Sadrita404/Open-Deck/Images/1.png

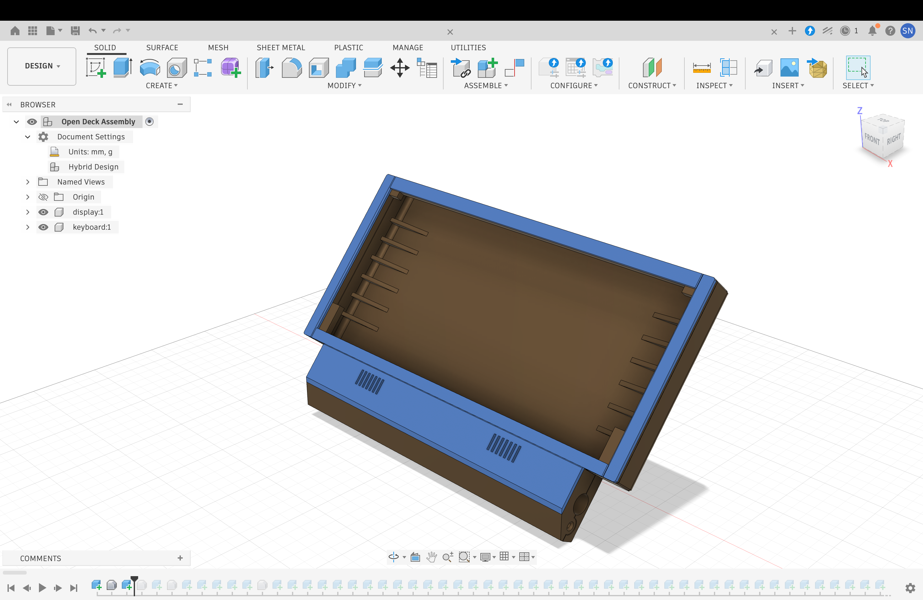
Images/1.png
