Sadrita404/Open-Deck/Images/2.png

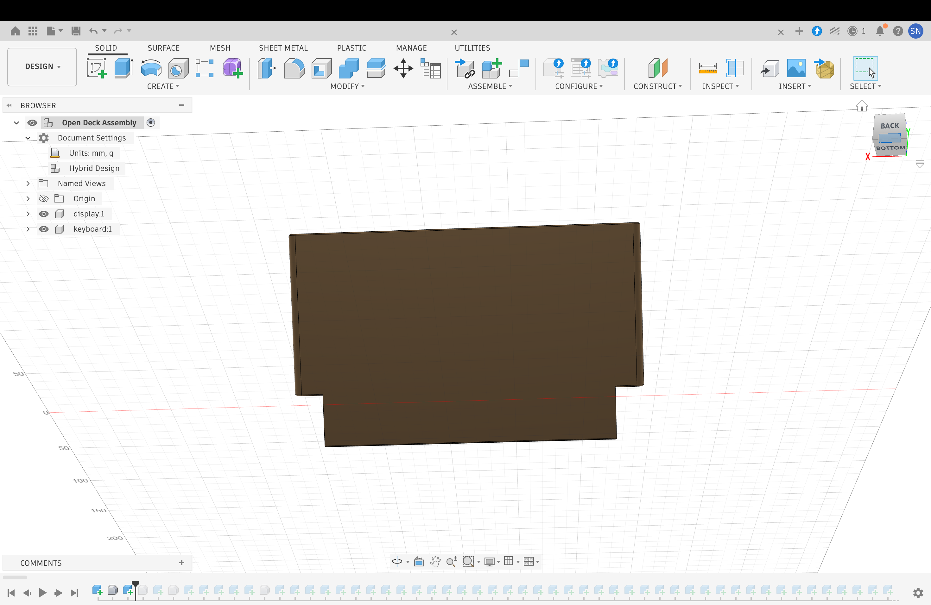
Images/2.png
