Sadrita404/Open-Deck/Images/3.png

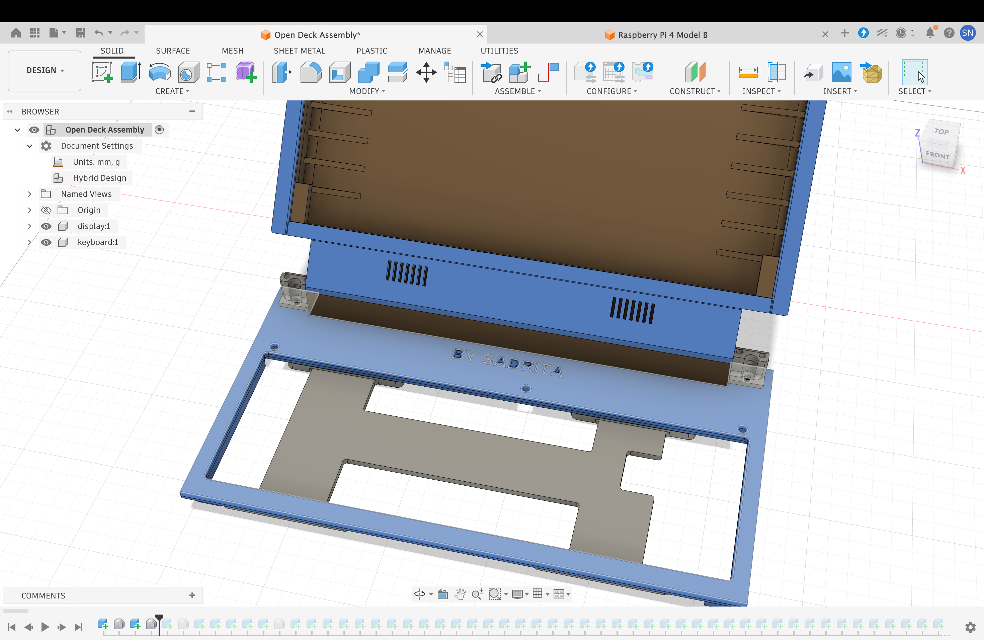
Images/3.png
