Sadrita404/Open-Deck/Images/4.png

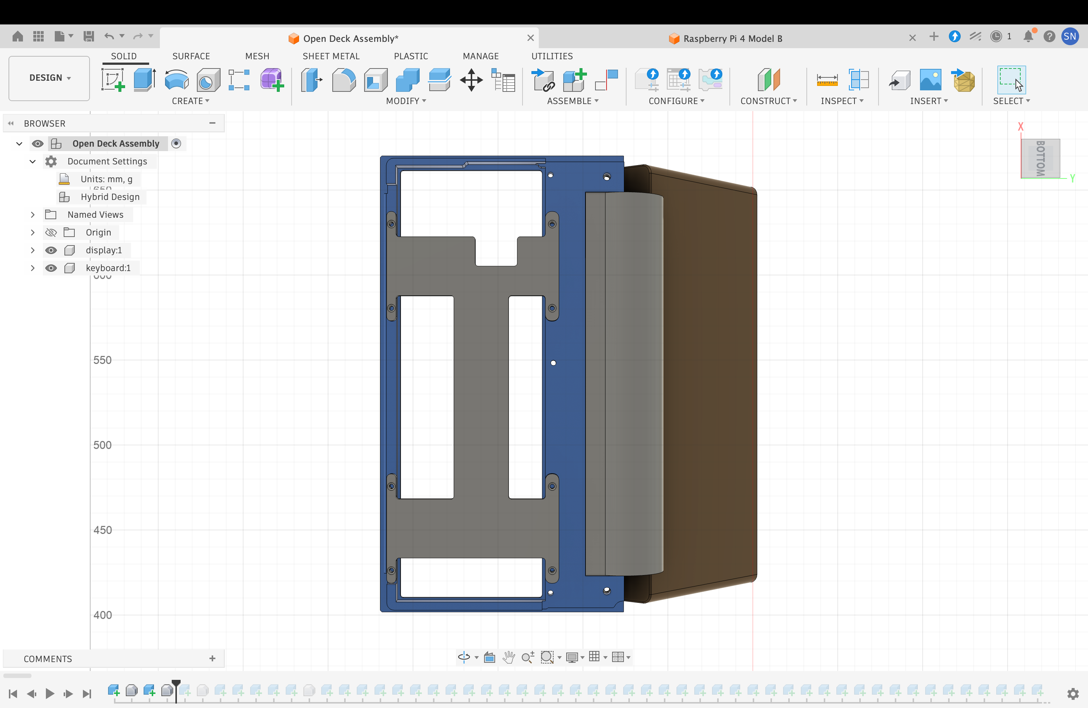
Images/4.png
