Sadrita404/Open-Deck/Images/5.png

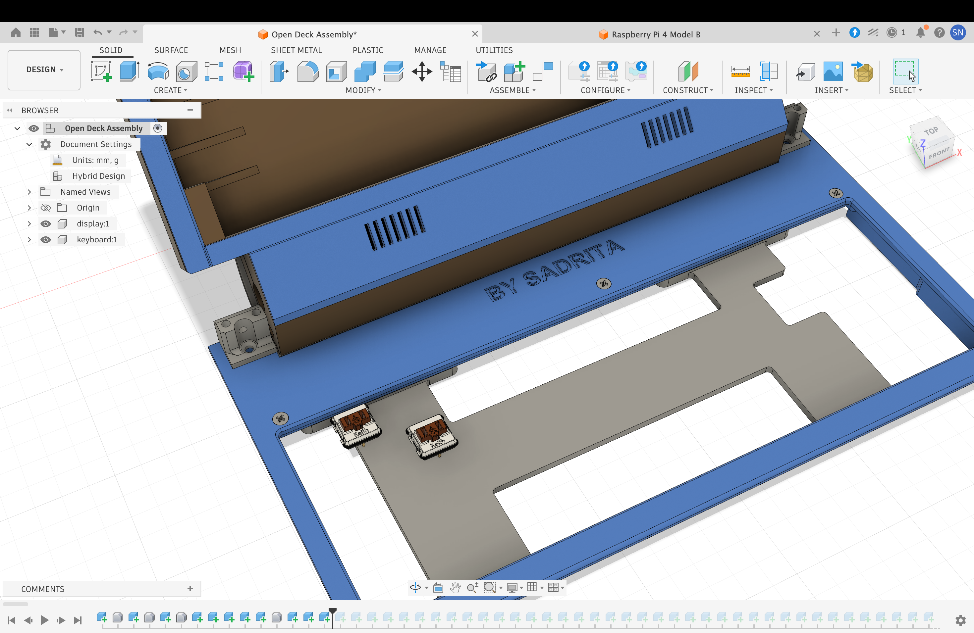
Images/5.png
