Sadrita404/Open-Deck/Images/6.png

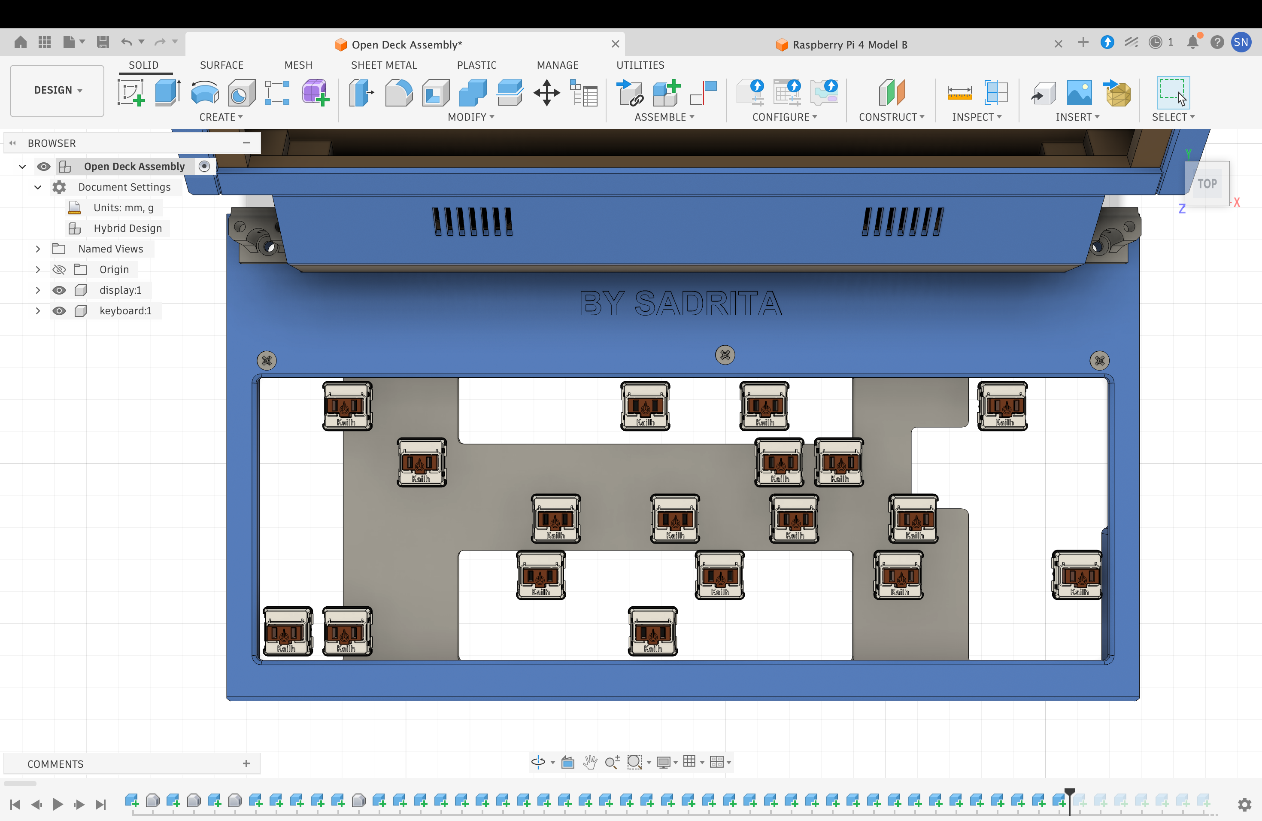
Images/6.png
