Sadrita404/Open-Deck/Images/7.png

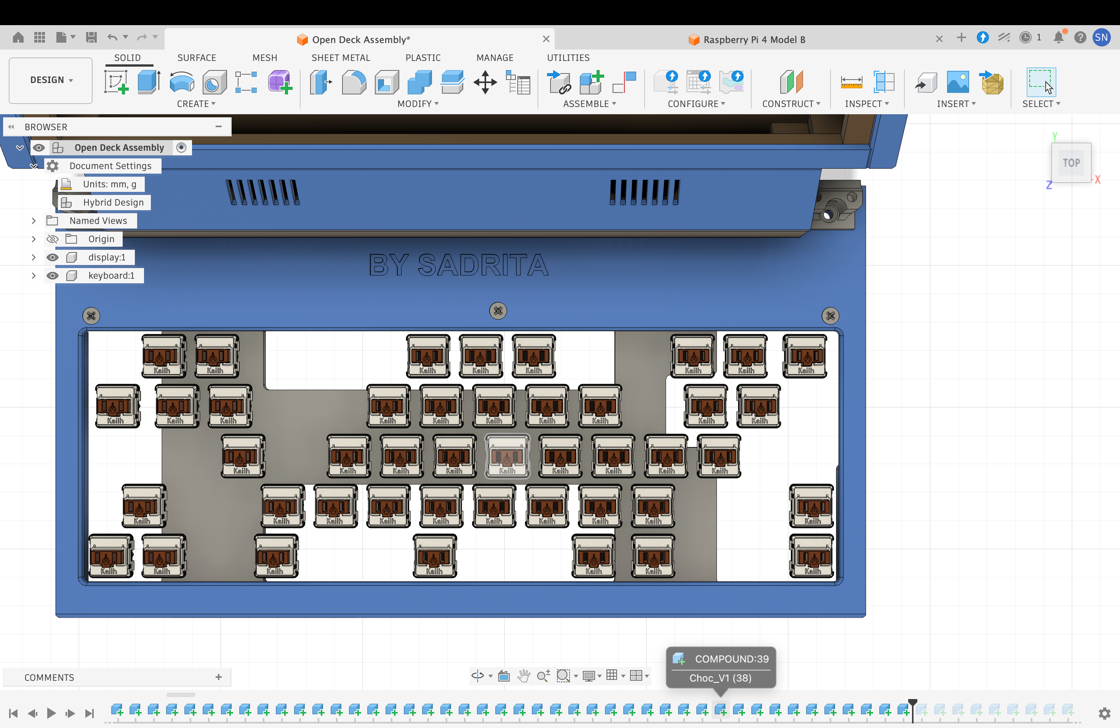
Images/7.png
