Sadrita404/Open-Deck/Images/8.png

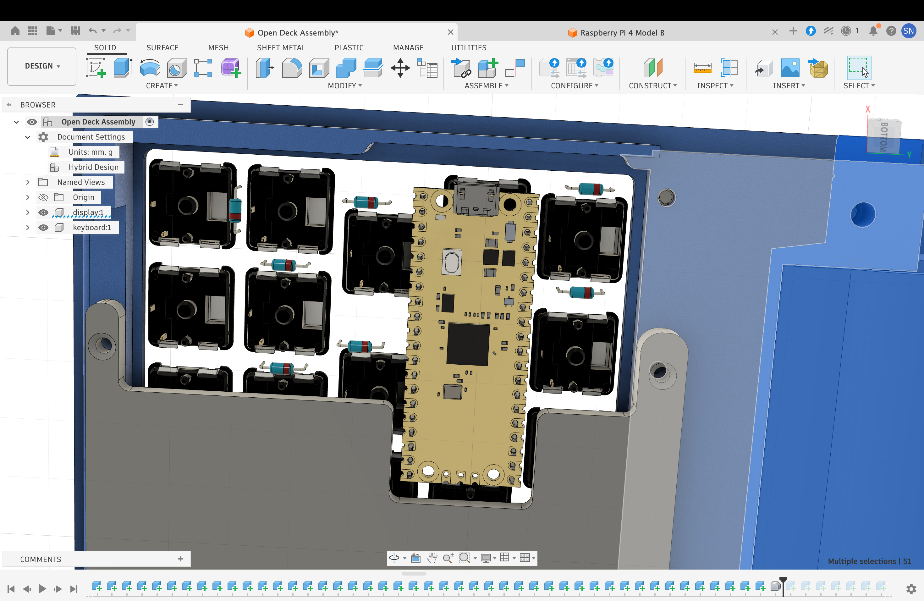
Images/8.png
