Sadrita404/Open-Deck/Images/9.png

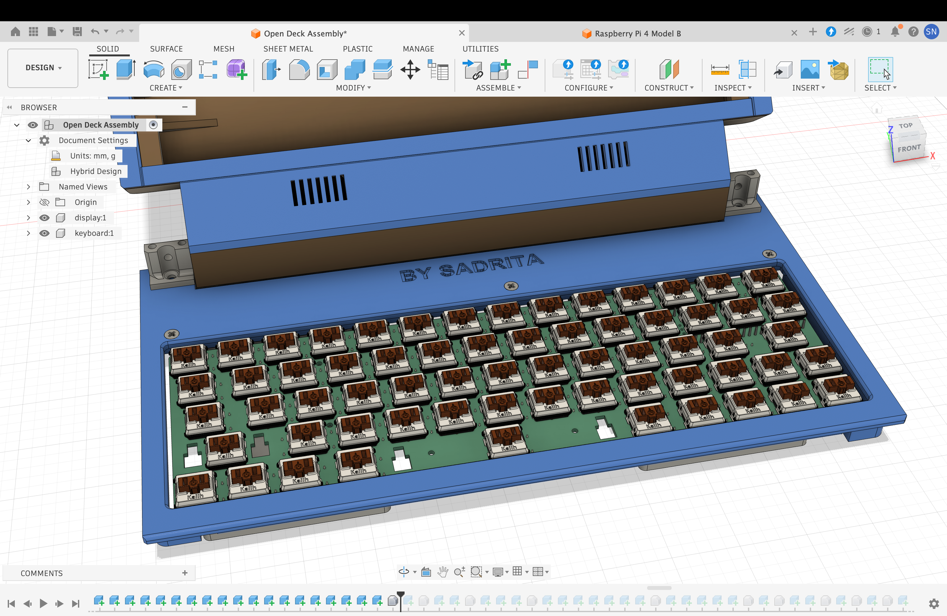
Images/9.png
