Sadrita404/Open-Deck/Images/10.png

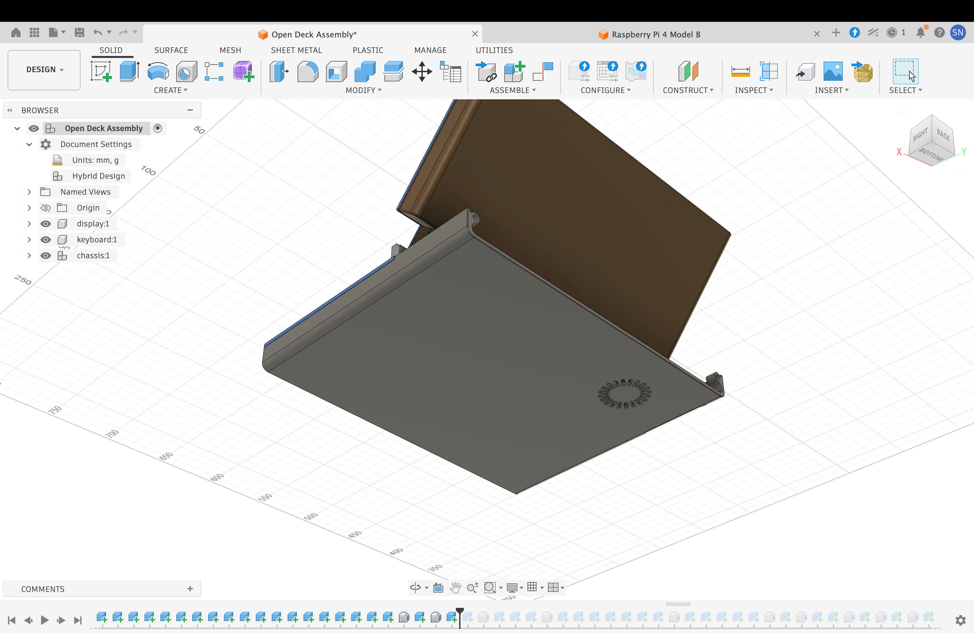
Images/10.png
