Sadrita404/Open-Deck/Images/11.png

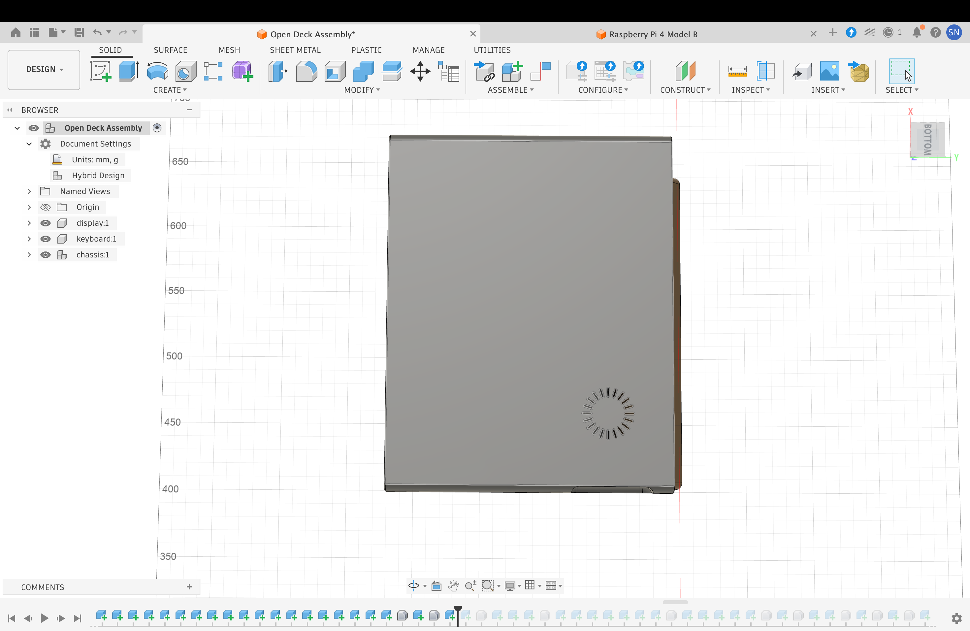
Images/11.png
