Sadrita404/Open-Deck/Images/12.png

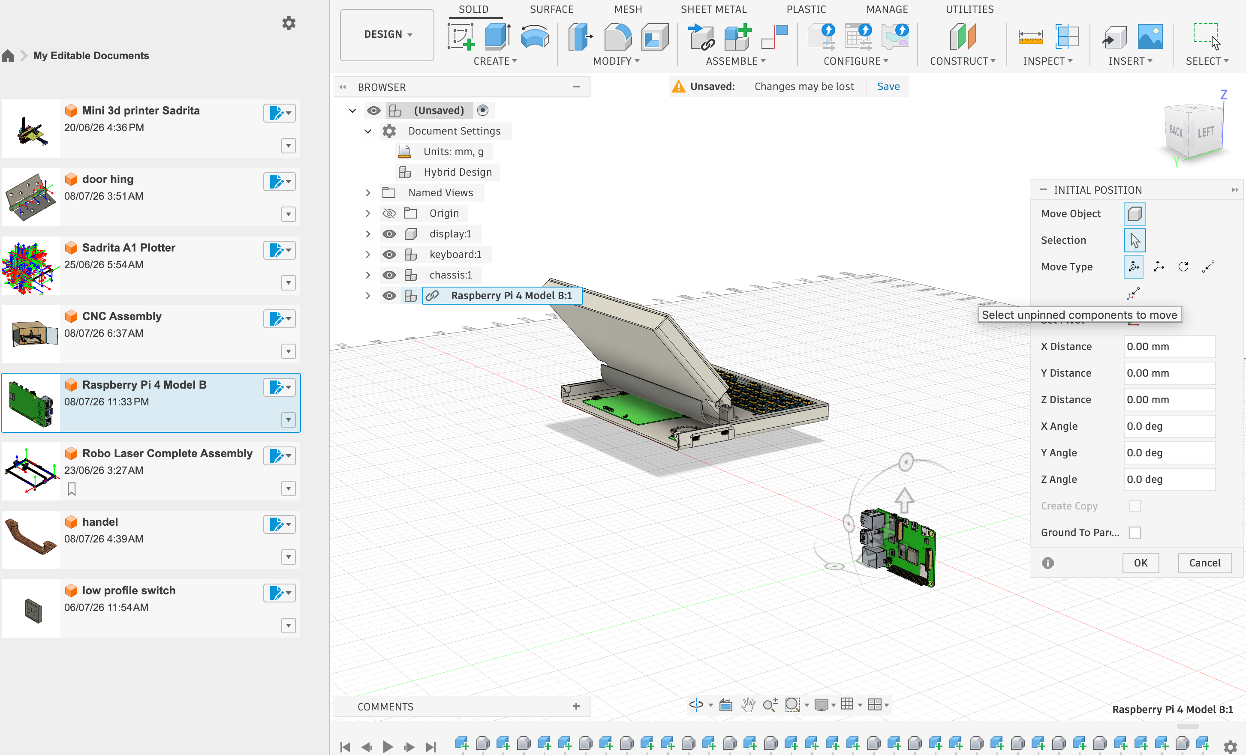
Images/12.png
