Sadrita404/Open-Deck/Images/13.png

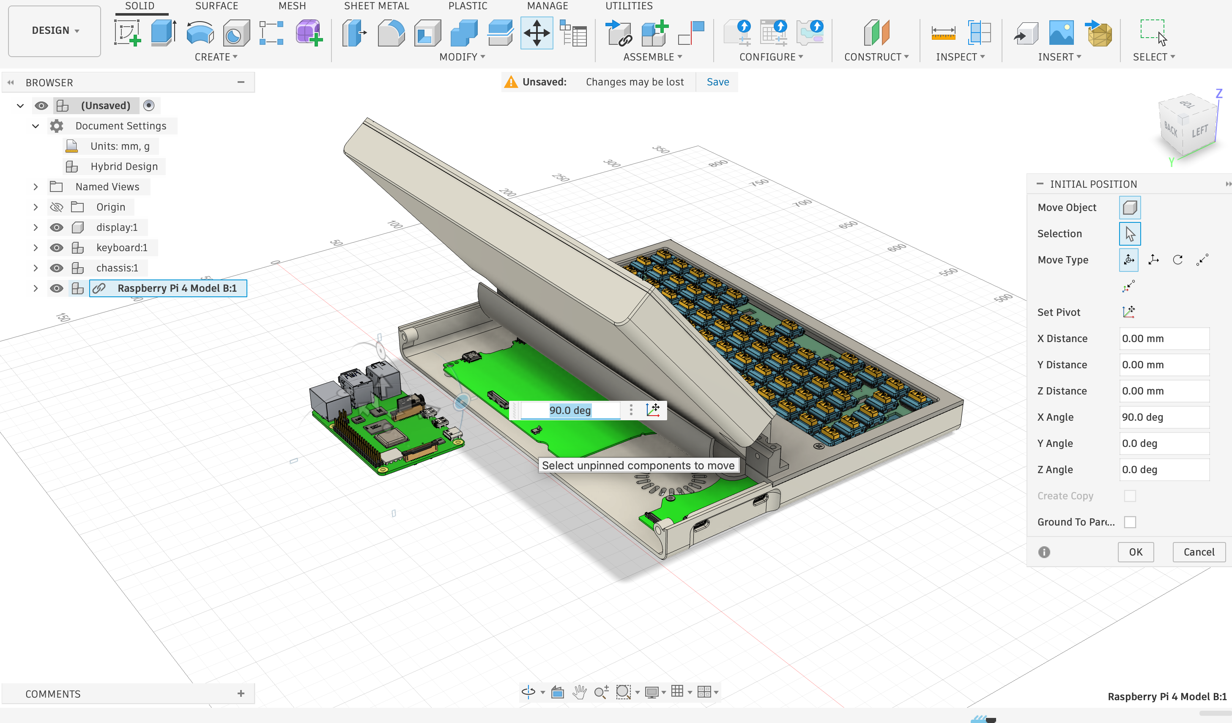
Images/13.png
