Sadrita404/Open-Deck/Images/14.png

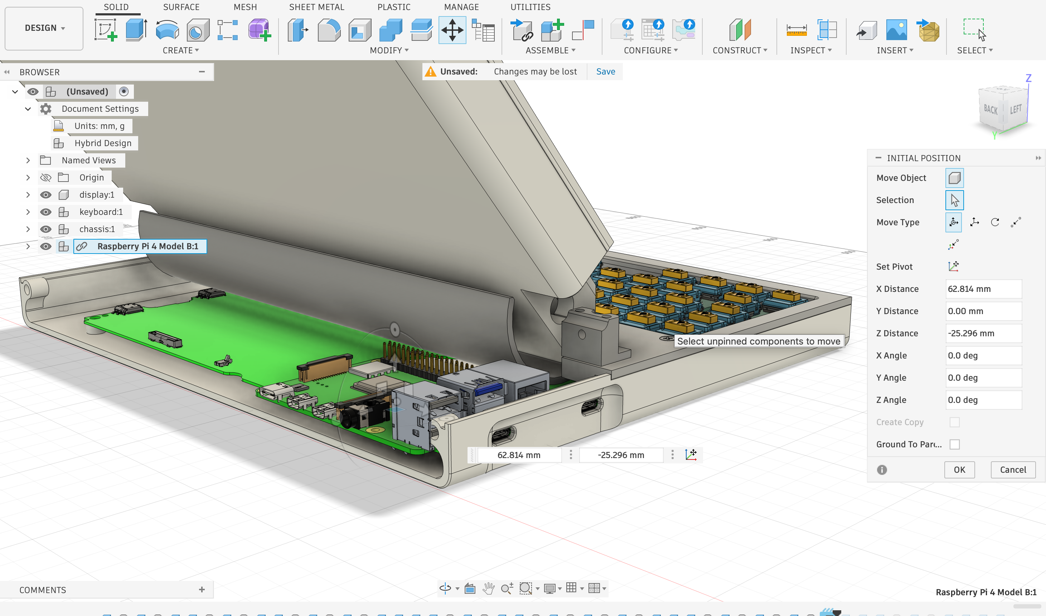
Images/14.png
