Sadrita404/Open-Deck/Images/15.png

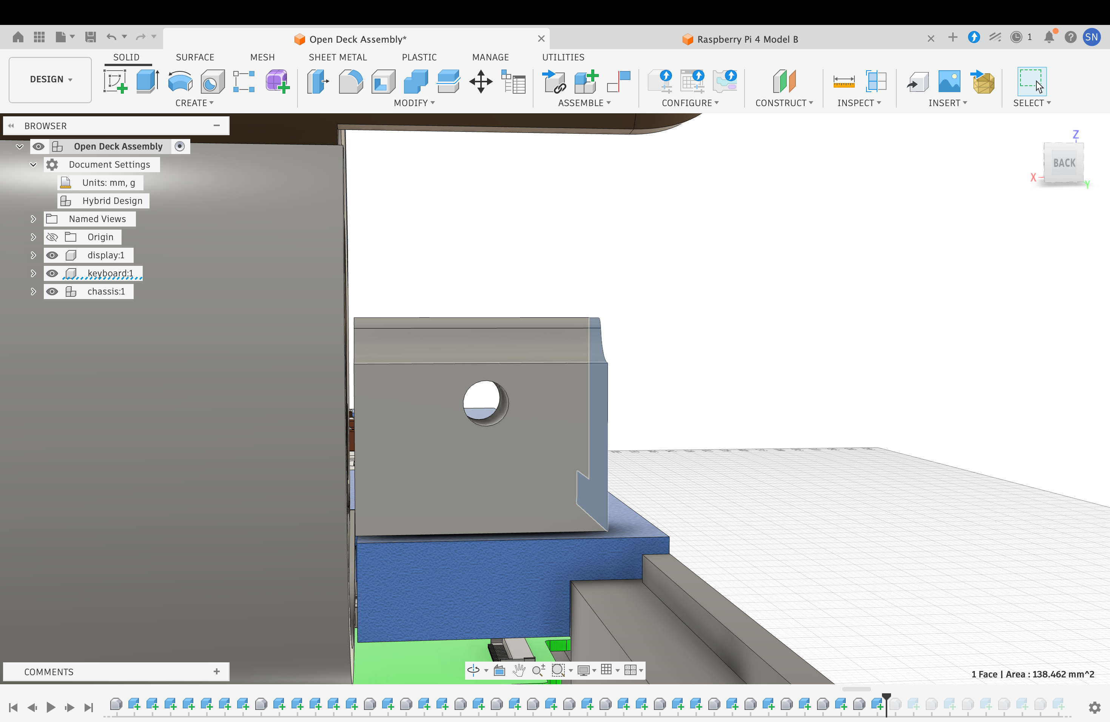
Images/15.png
