Sadrita404/Open-Deck/Images/16.png

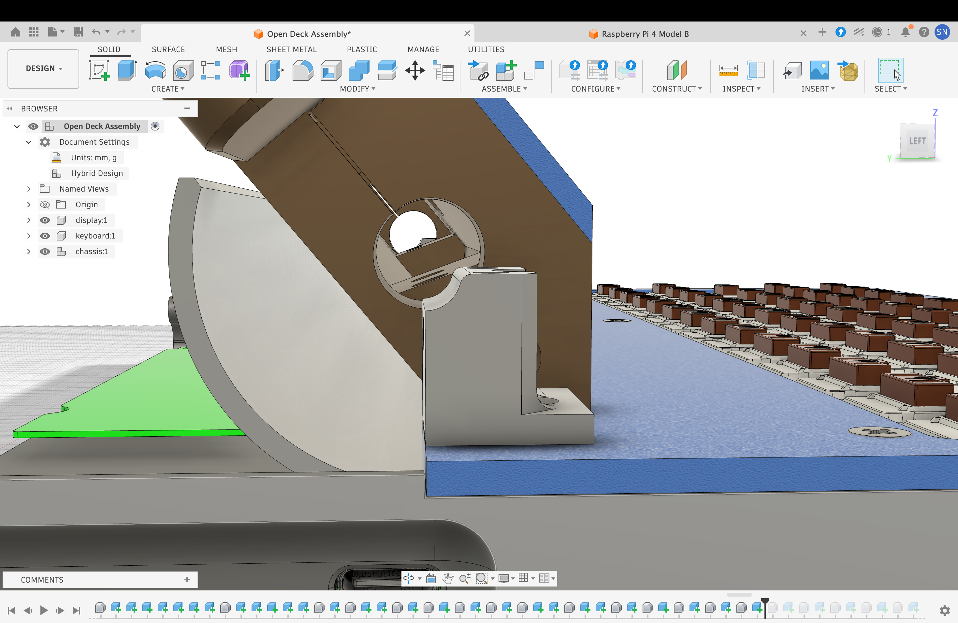
Images/16.png
