Sadrita404/Open-Deck/Images/17.png

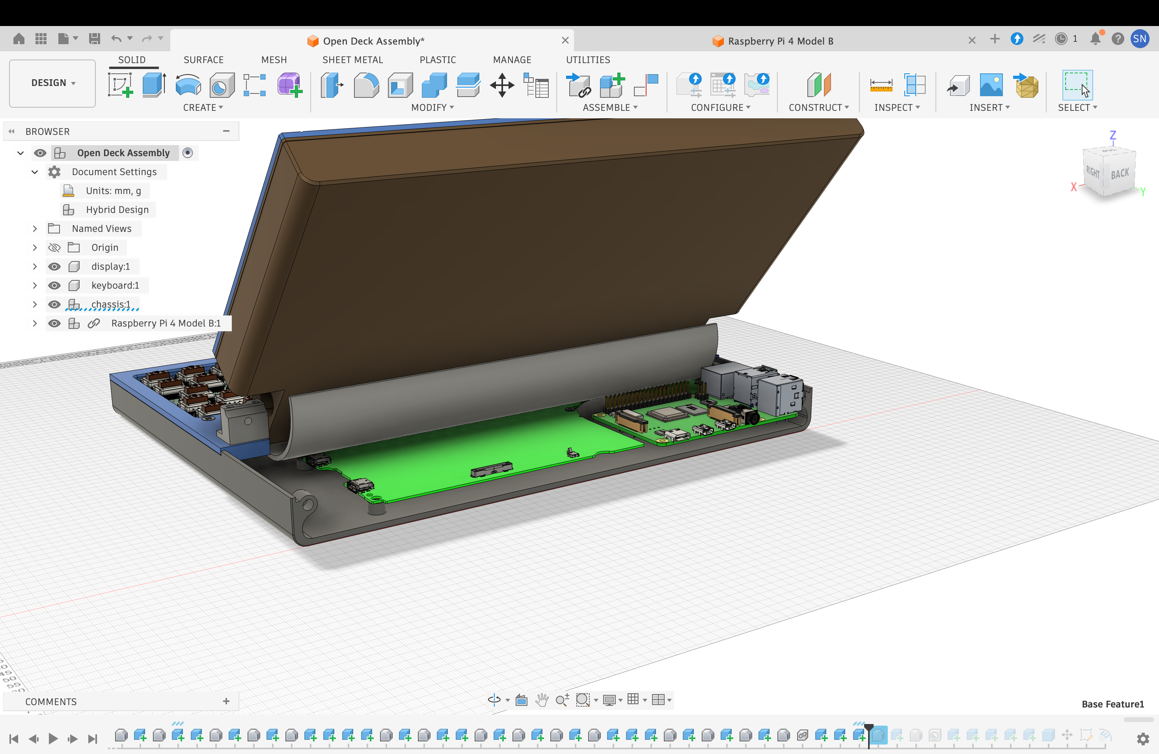
Images/17.png
