Sadrita404/Open-Deck/Images/18.png

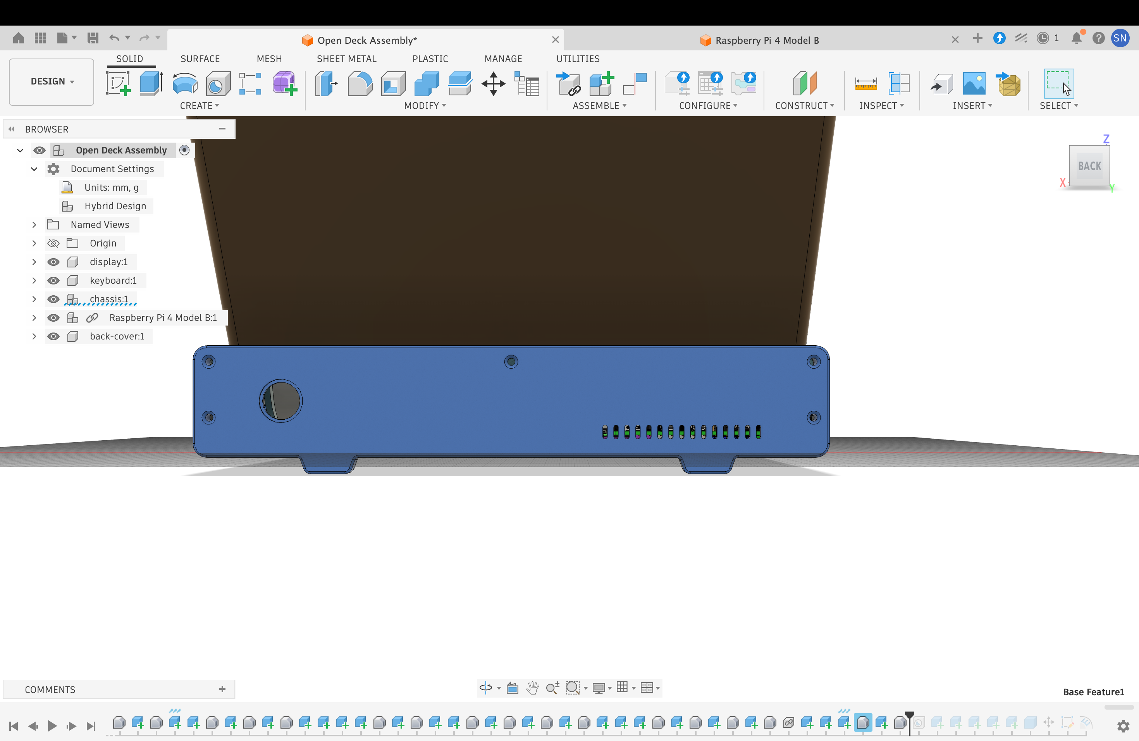
Images/18.png
