Sadrita404/Open-Deck/Images/19.png

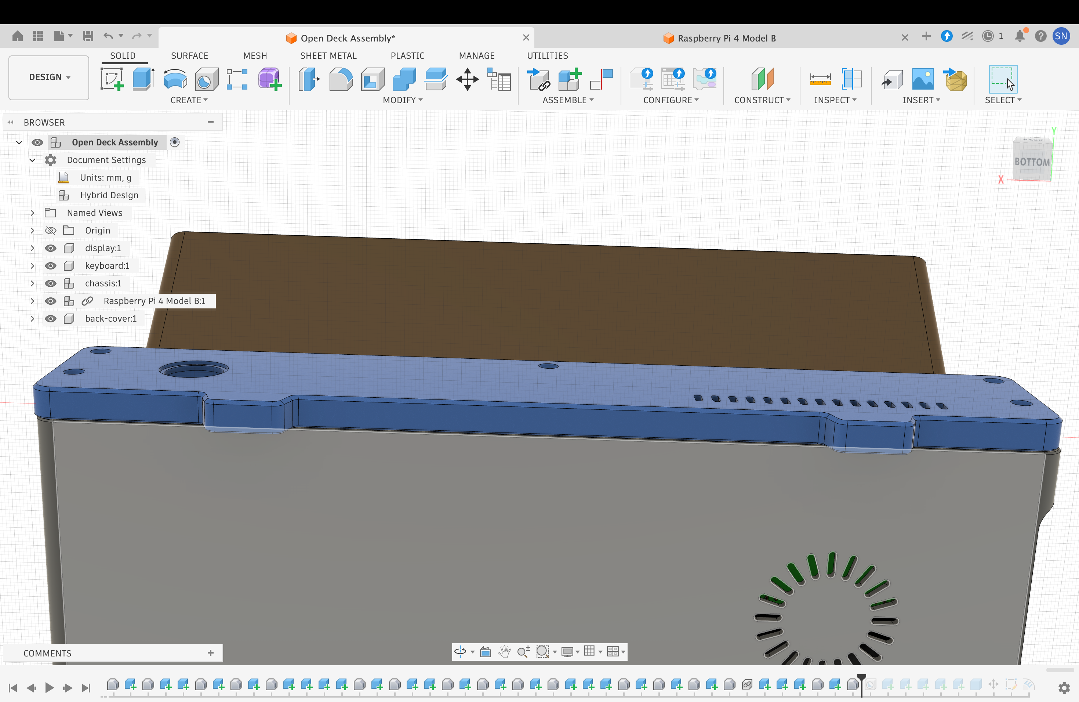
Images/19.png
