Sadrita404/Open-Deck/Images/20.png

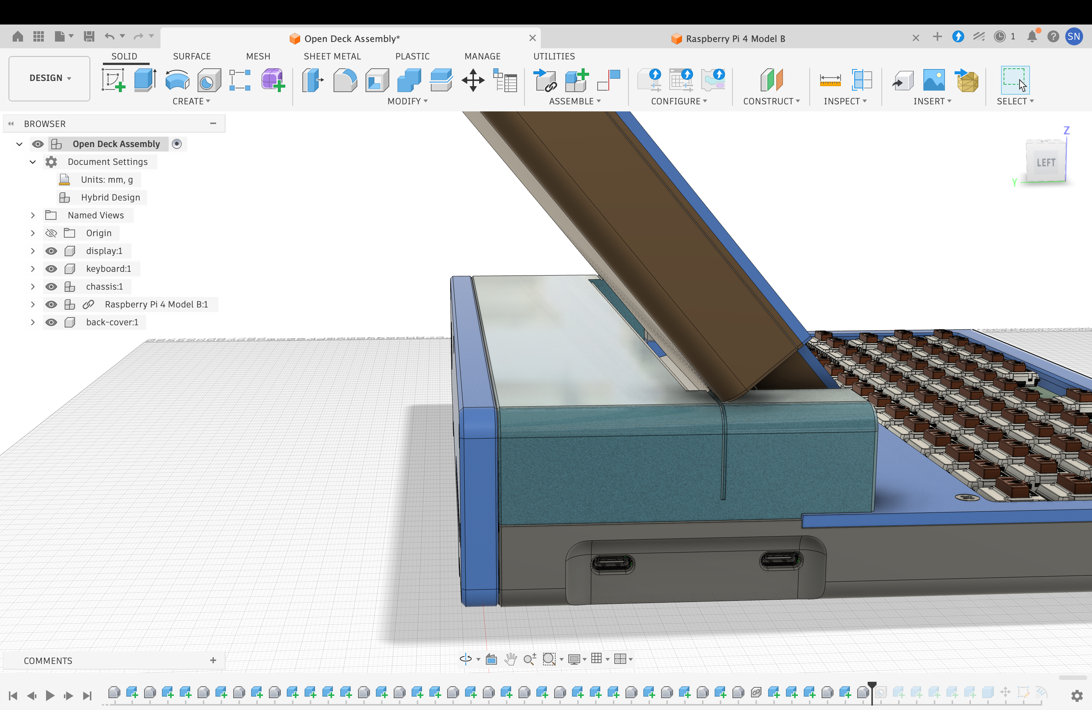
Images/20.png
