Sadrita404/Open-Deck/Images/22.png

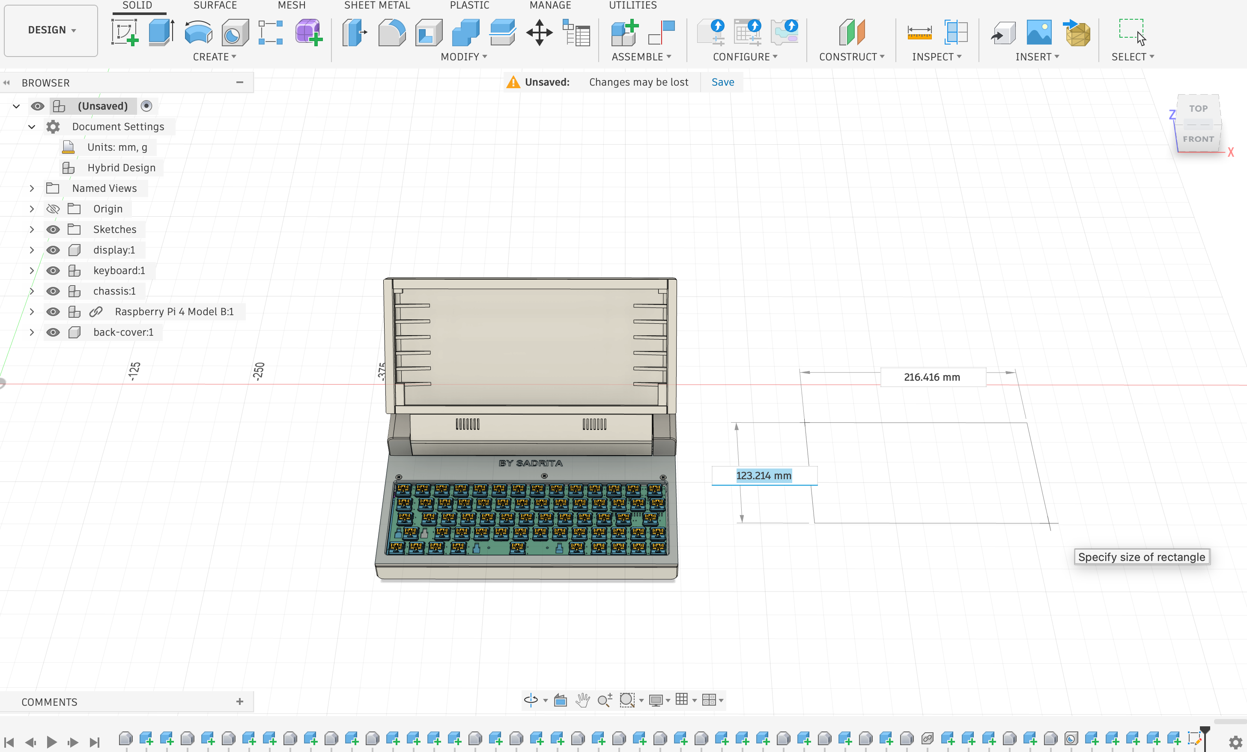
Images/22.png
