Sadrita404/Open-Deck/Images/23.png

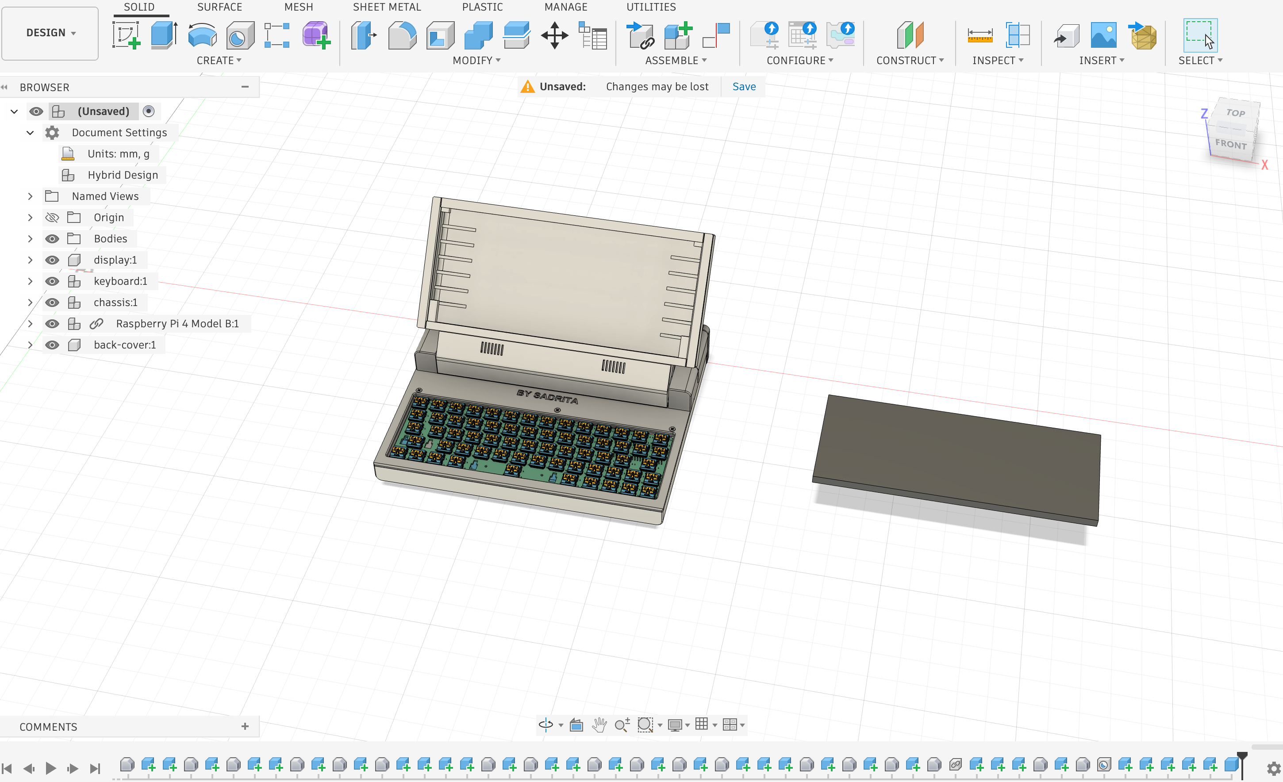
Images/23.png
