Sadrita404/Open-Deck/Images/24.png

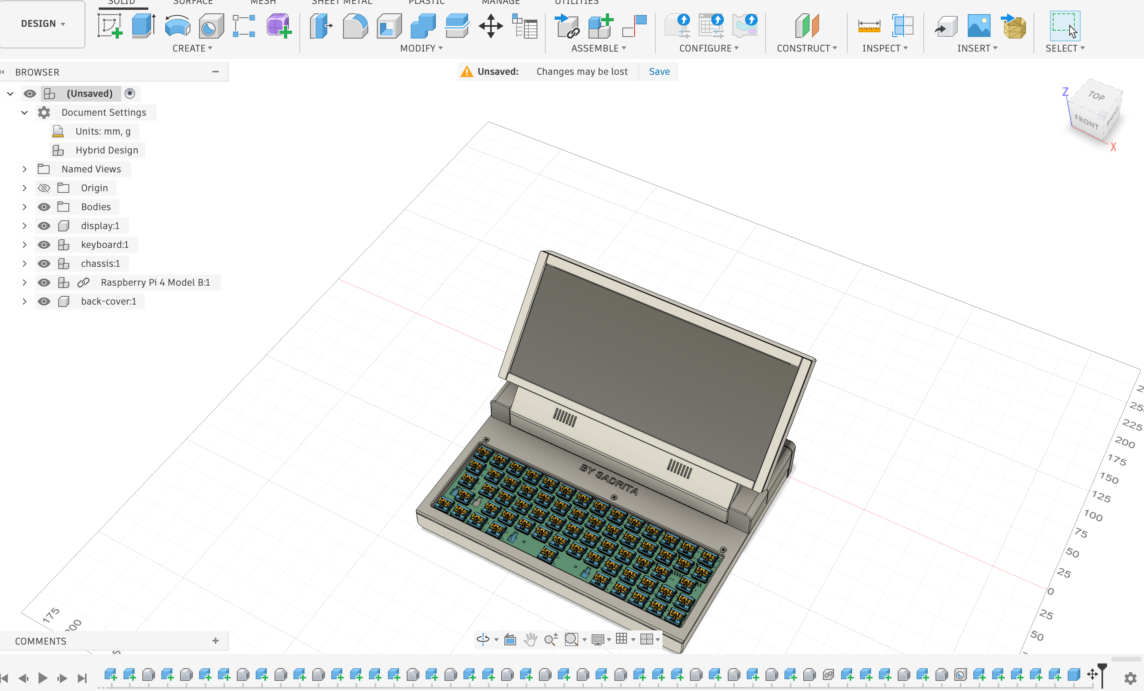
Images/24.png
