Sadrita404/Open-Deck/Images/25.png

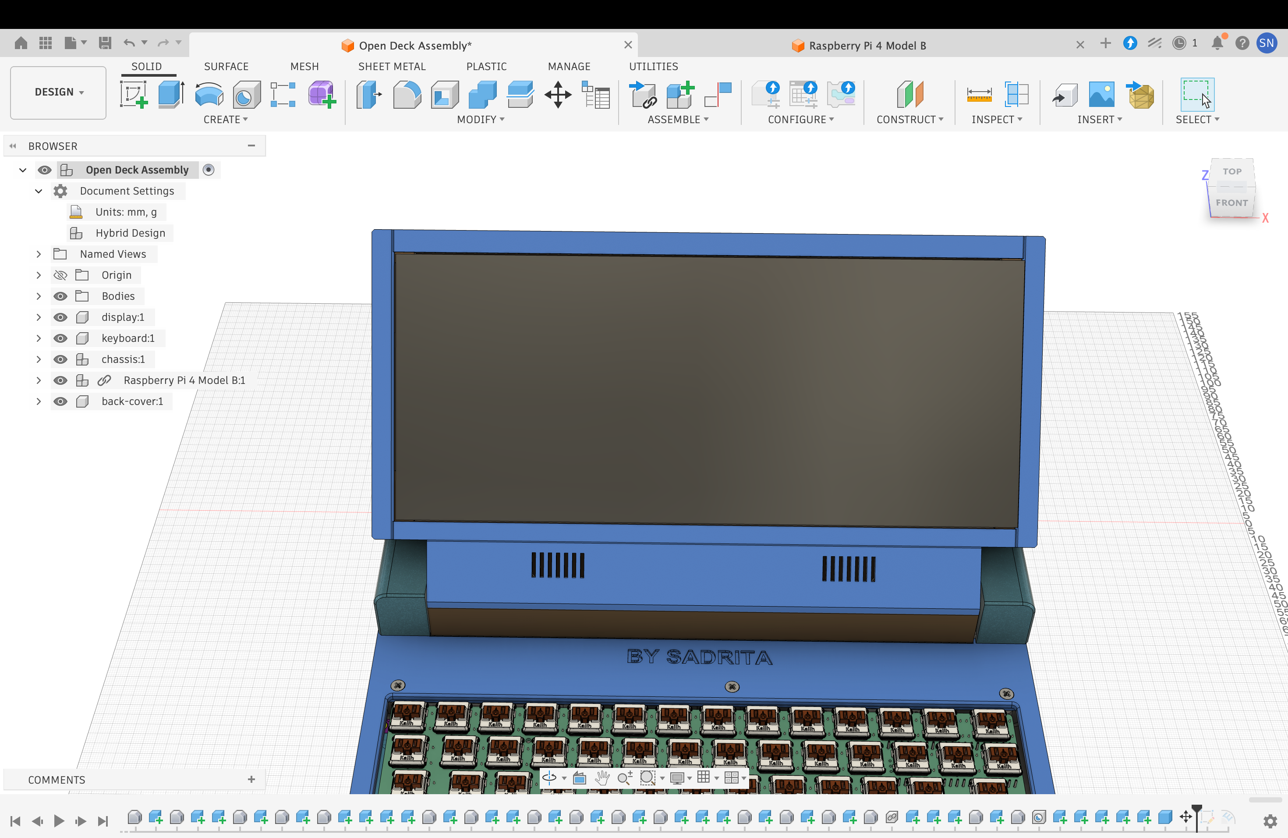
Images/25.png
