Sadrita404/Open-Deck/Images/26.png

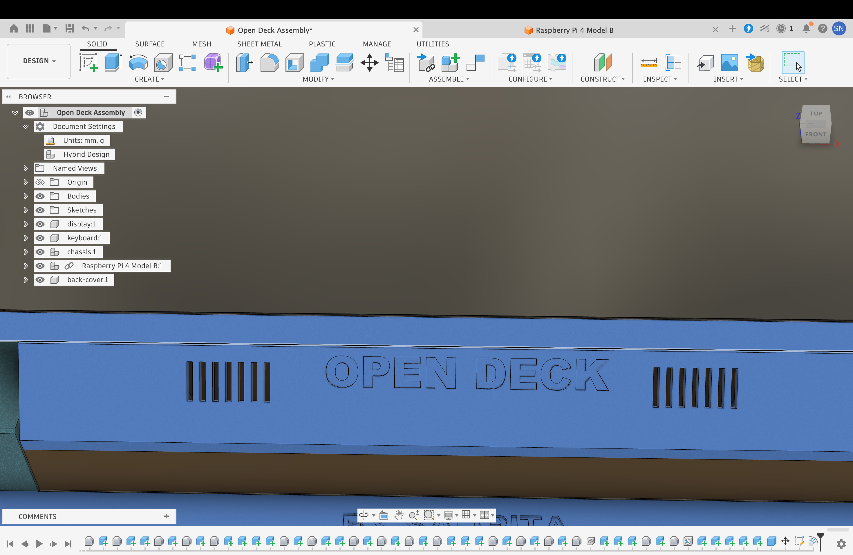
Images/26.png
