Sadrita404/Open-Deck/Images/27.png

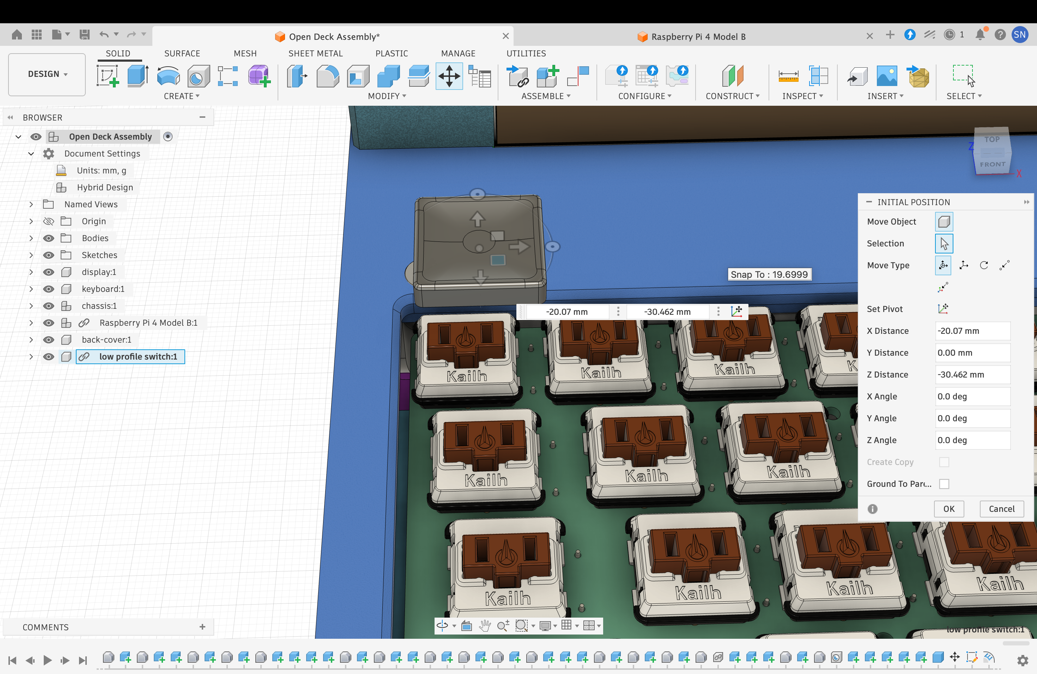
Images/27.png
