Sadrita404/Open-Deck/Images/29.png

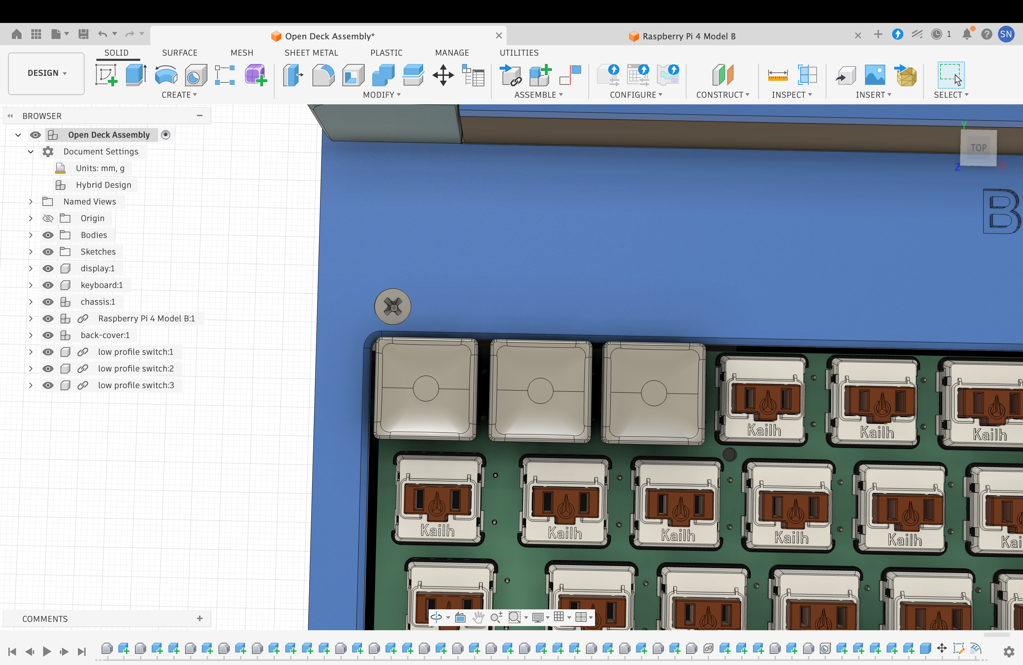
Images/29.png
