Sadrita404/Open-Deck/Images/30.png

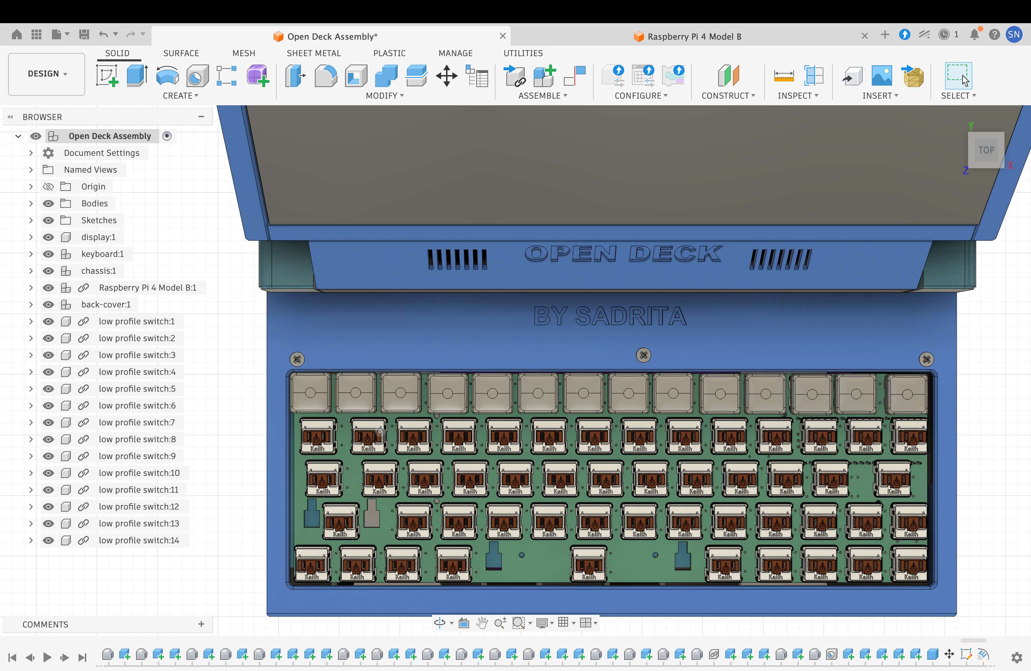
Images/30.png
