Sadrita404/Open-Deck/Images/31.png

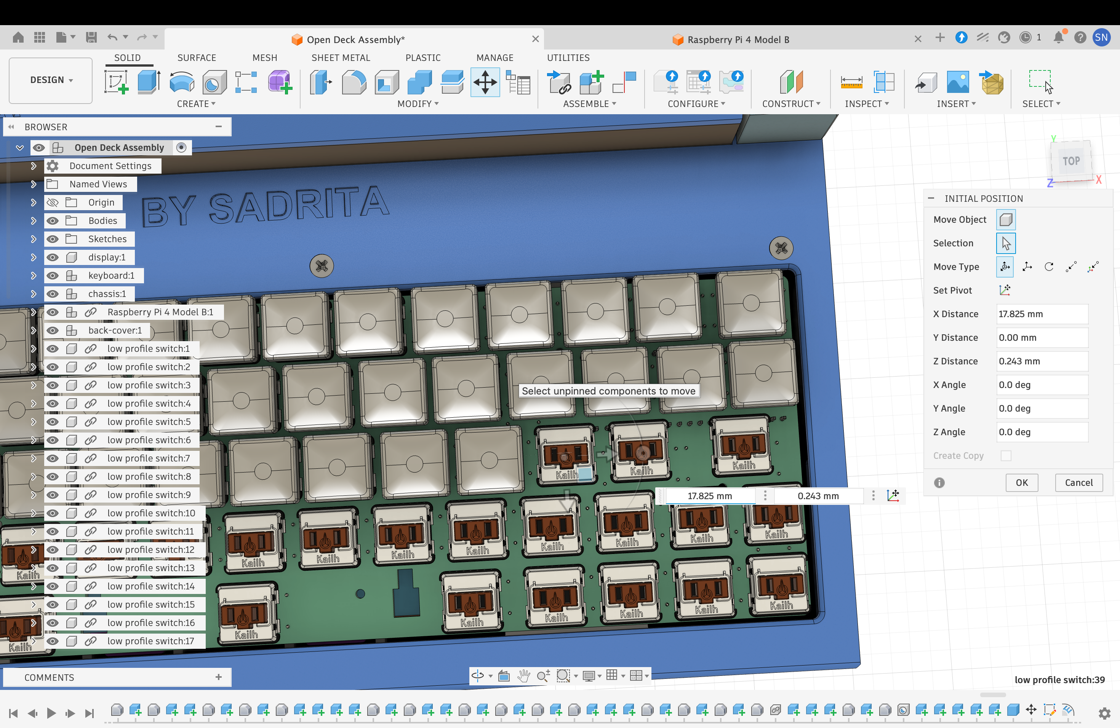
Images/31.png
