Sadrita404/Open-Deck/Images/32.png

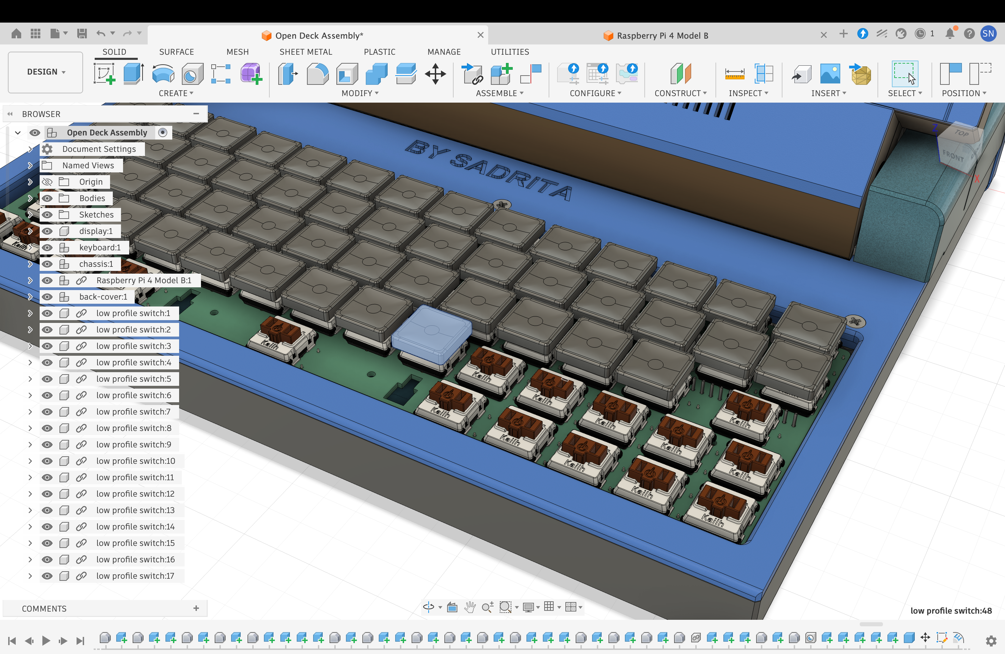
Images/32.png
