Sadrita404/Open-Deck/Images/33.png

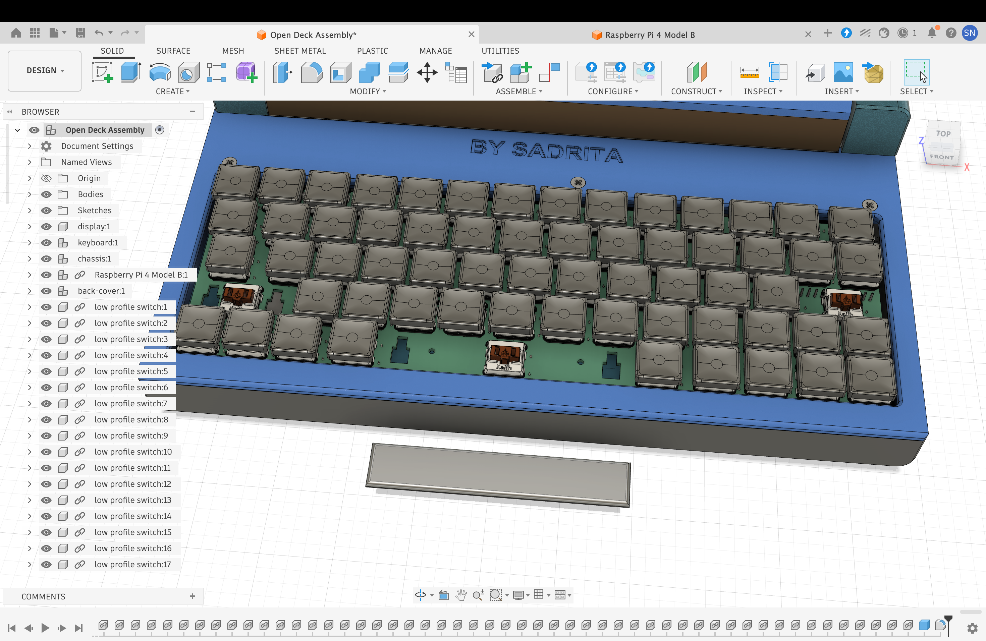
Images/33.png
