Sadrita404/Open-Deck/Images/34.png

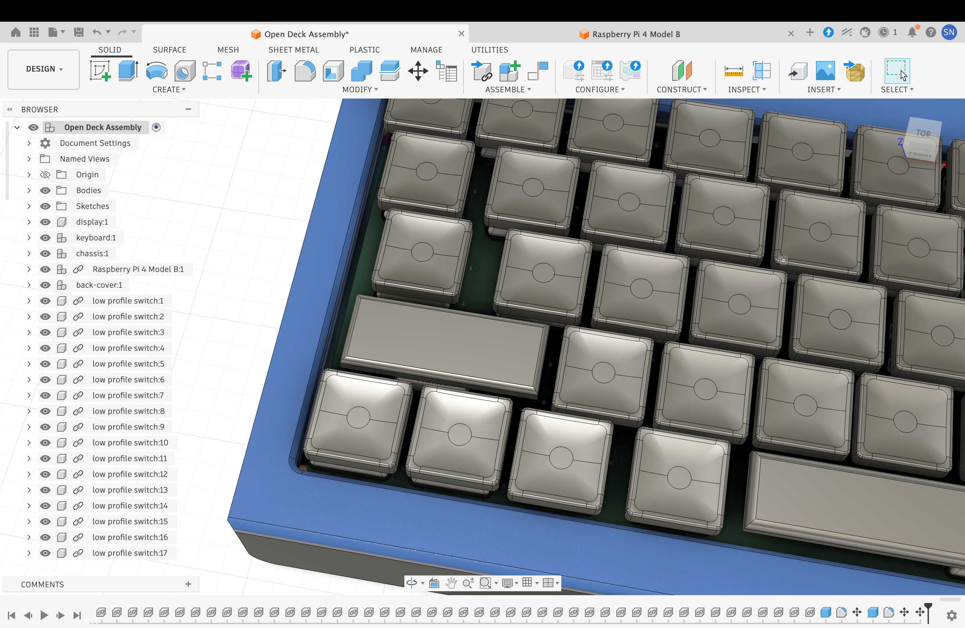
Images/34.png
