Sadrita404/Open-Deck/Images/35.png

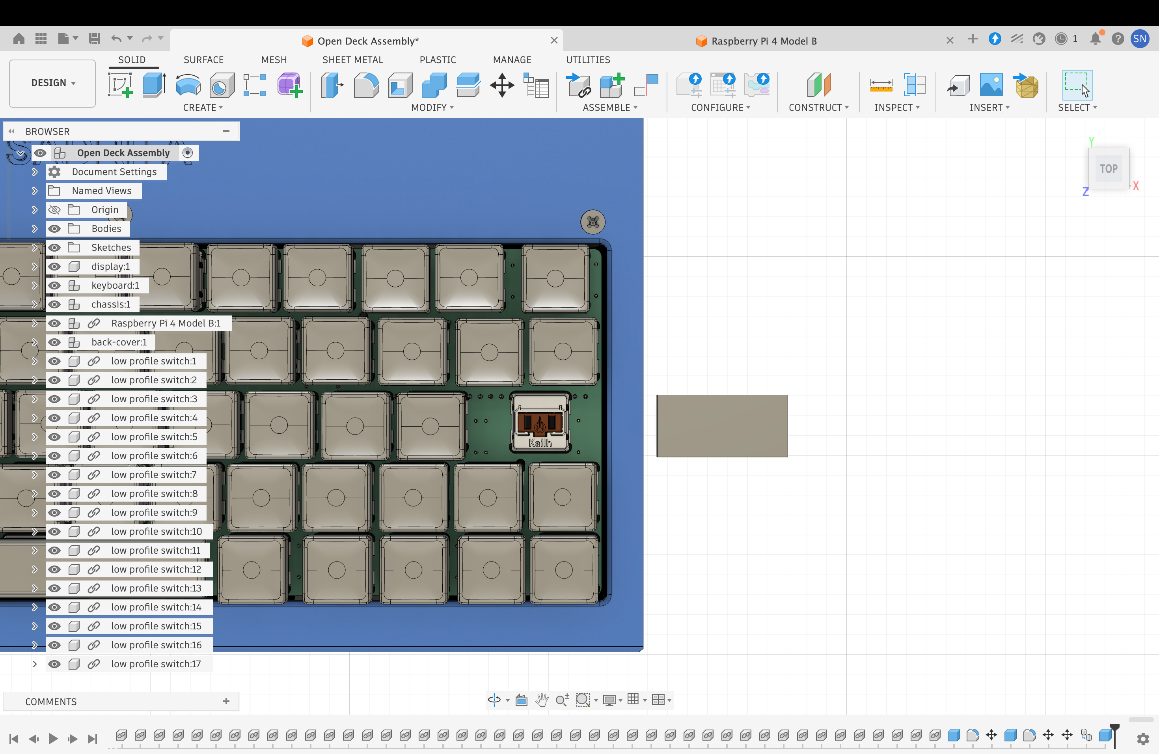
Images/35.png
