Sadrita404/Open-Deck/Images/36.png

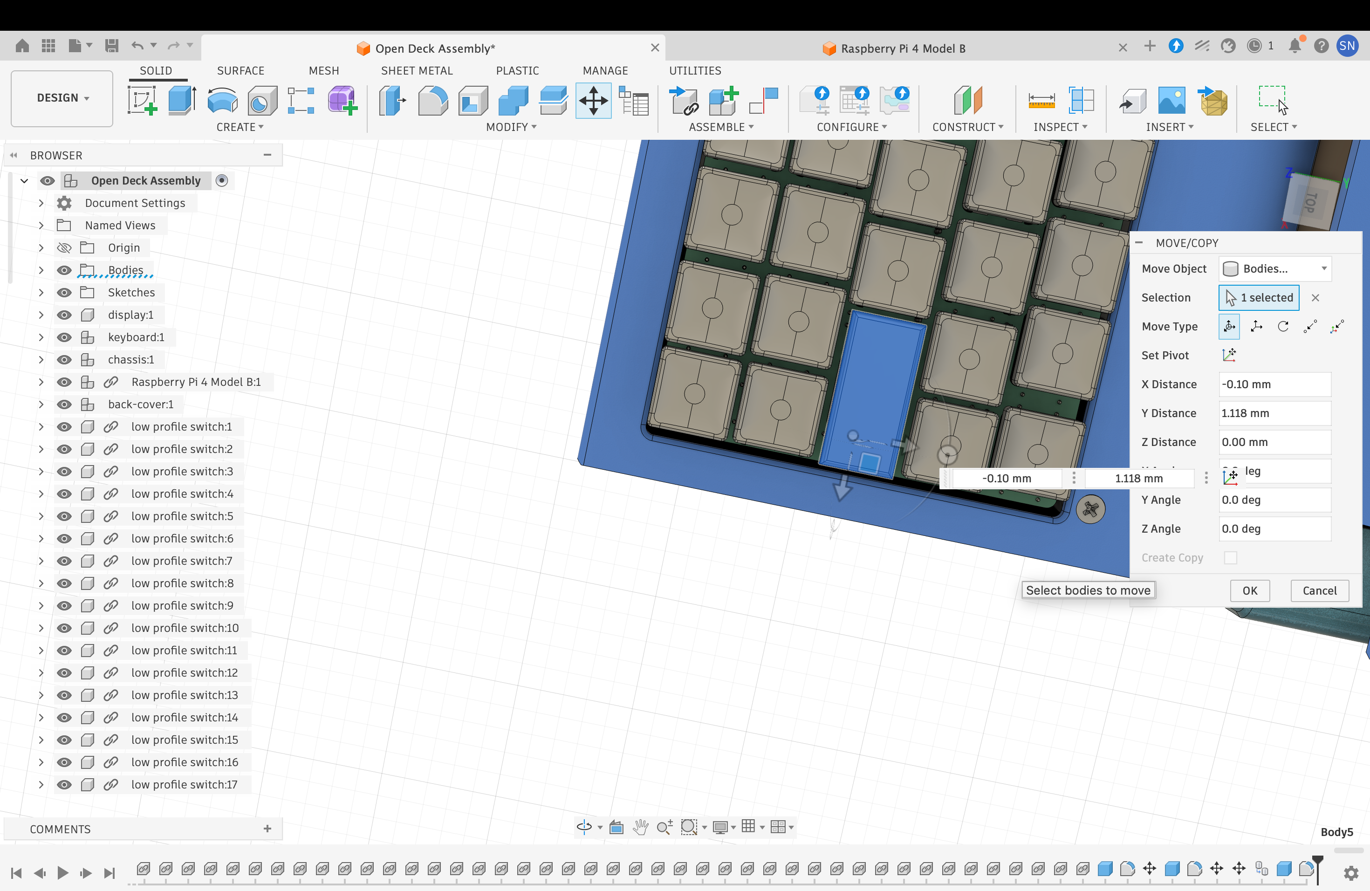
Images/36.png
