Sadrita404/Open-Deck/Images/37.png

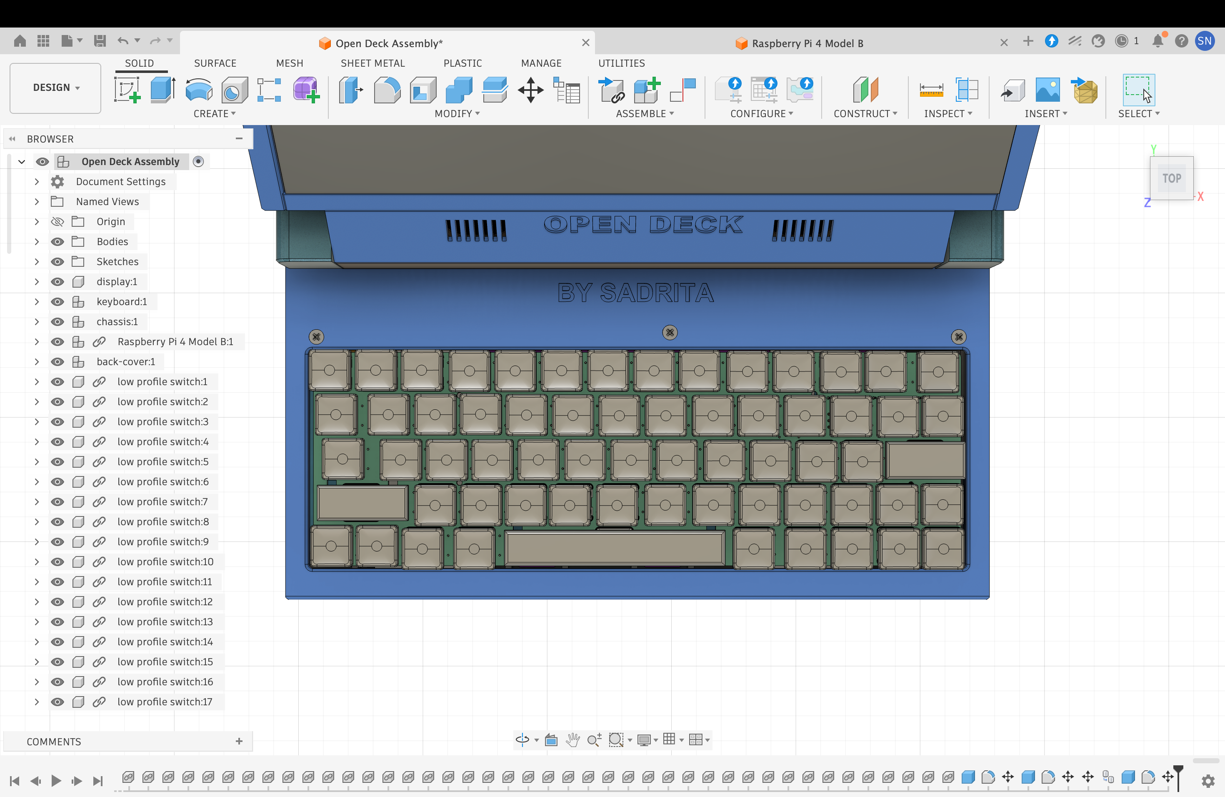
Images/37.png
