Sadrita404/Open-Deck/Images/38.png

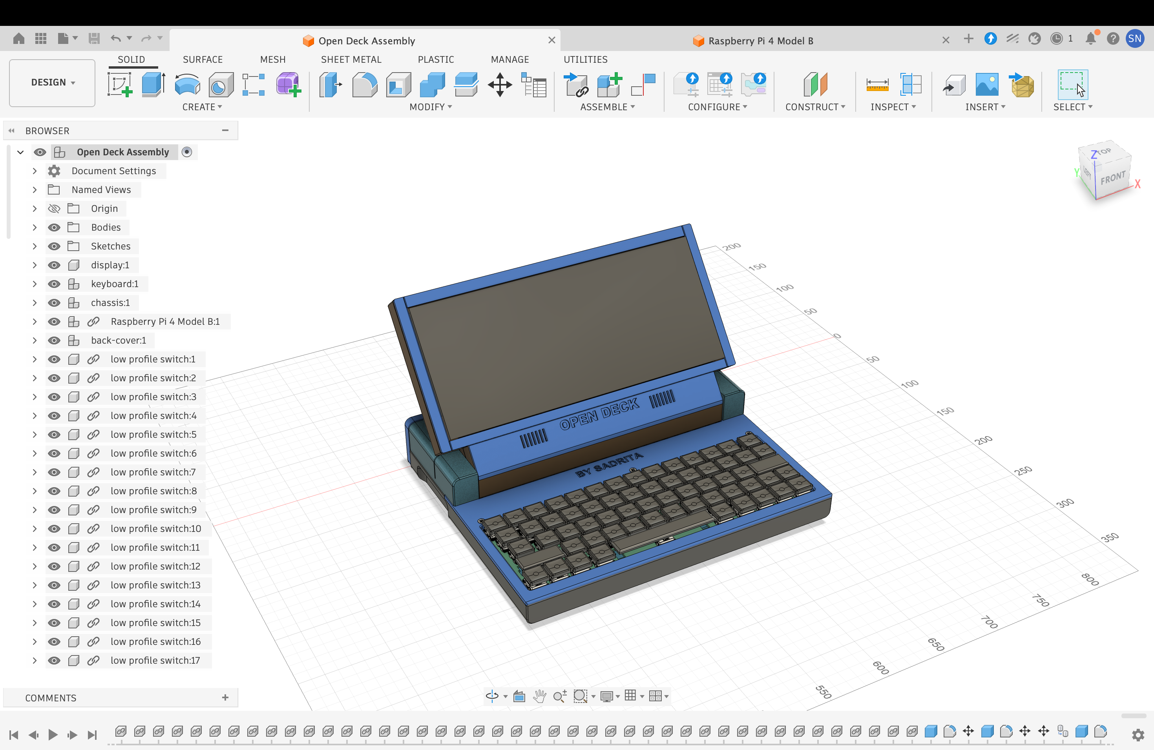
Images/38.png
