Sadrita404/Open-Deck/Images/39.png

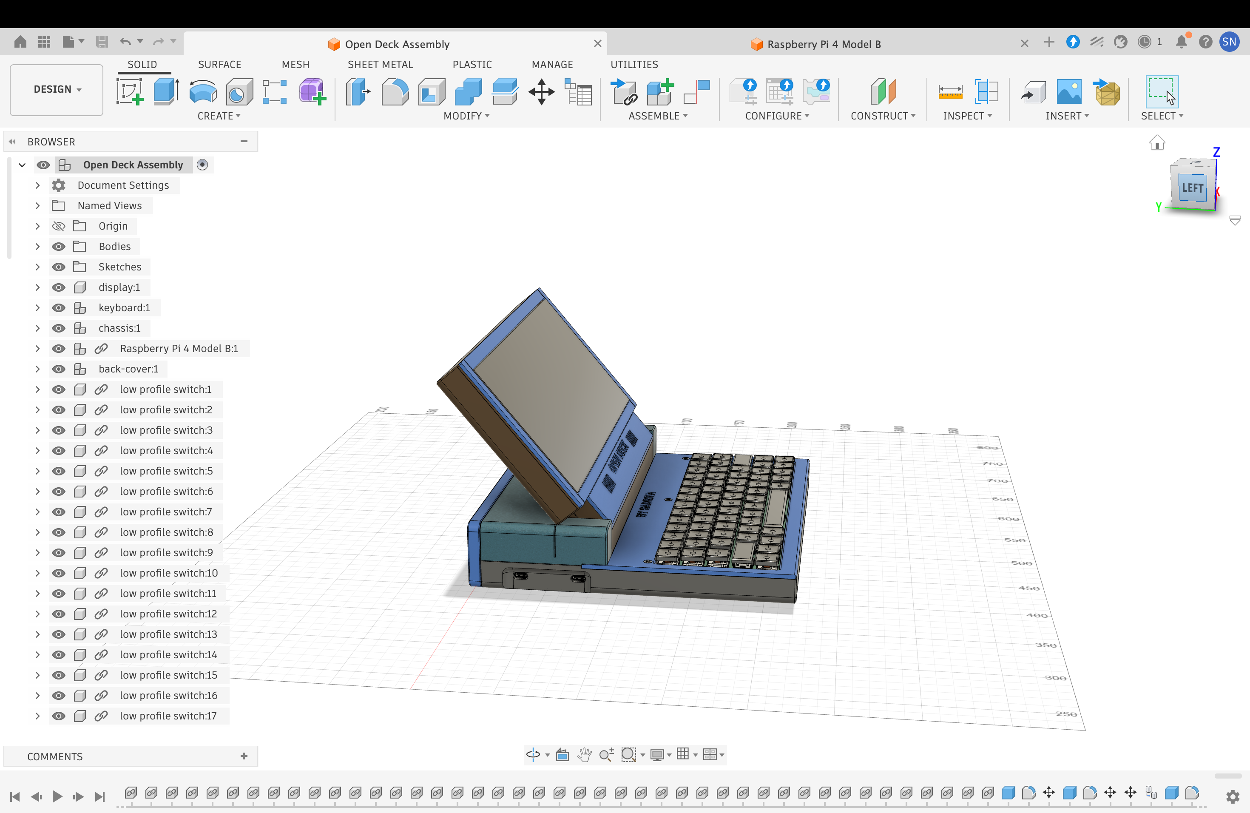
Images/39.png
