Sadrita404/Open-Deck/Images/40.png

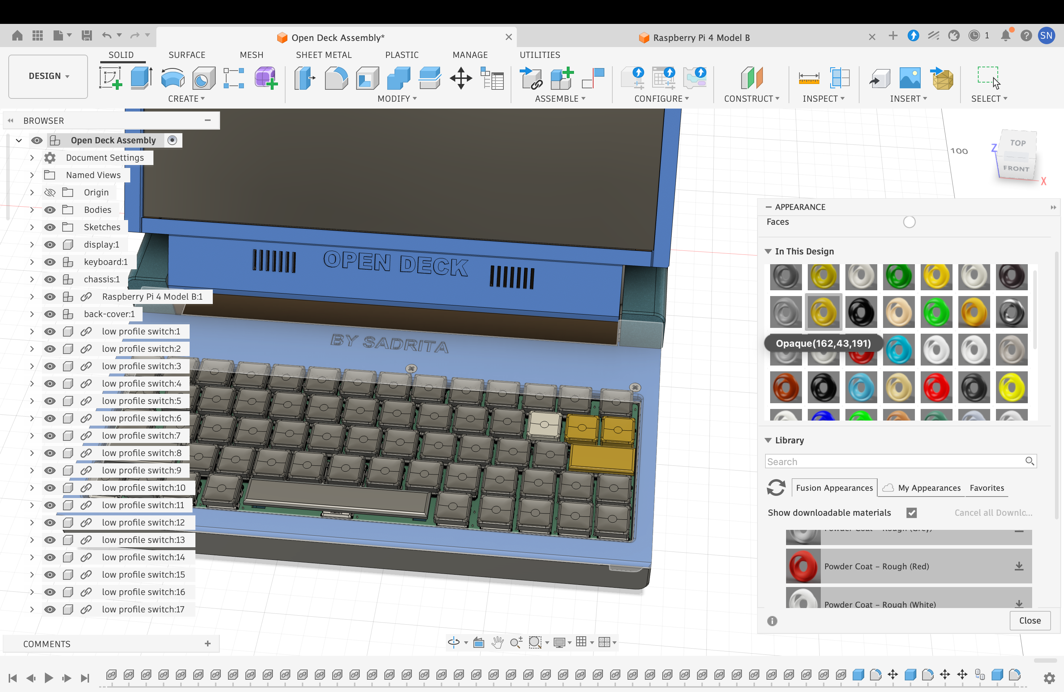
Images/40.png
