Sadrita404/Open-Deck/Images/41.png

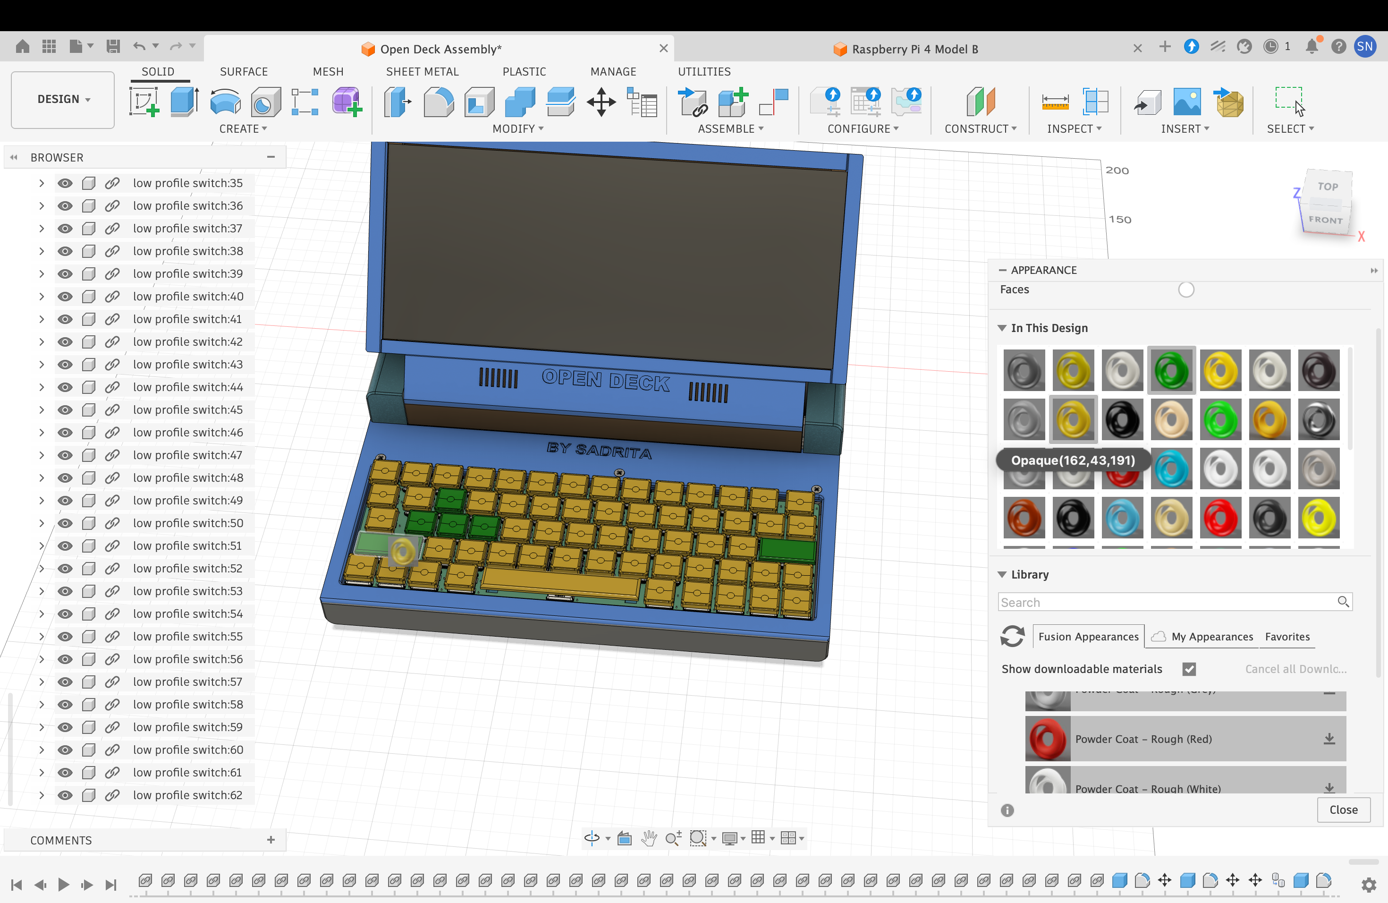
Images/41.png
