Sadrita404/Open-Deck/Images/42.png

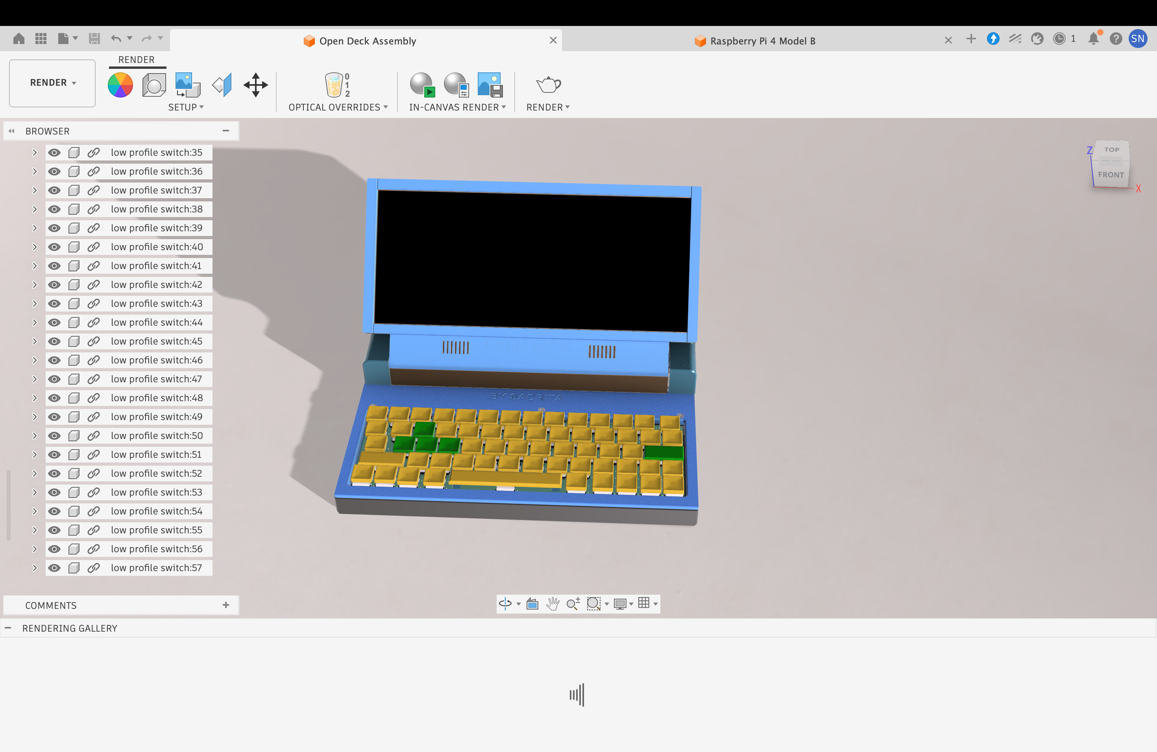
Images/42.png
