Sadrita404/Open-Deck/Images/44.png

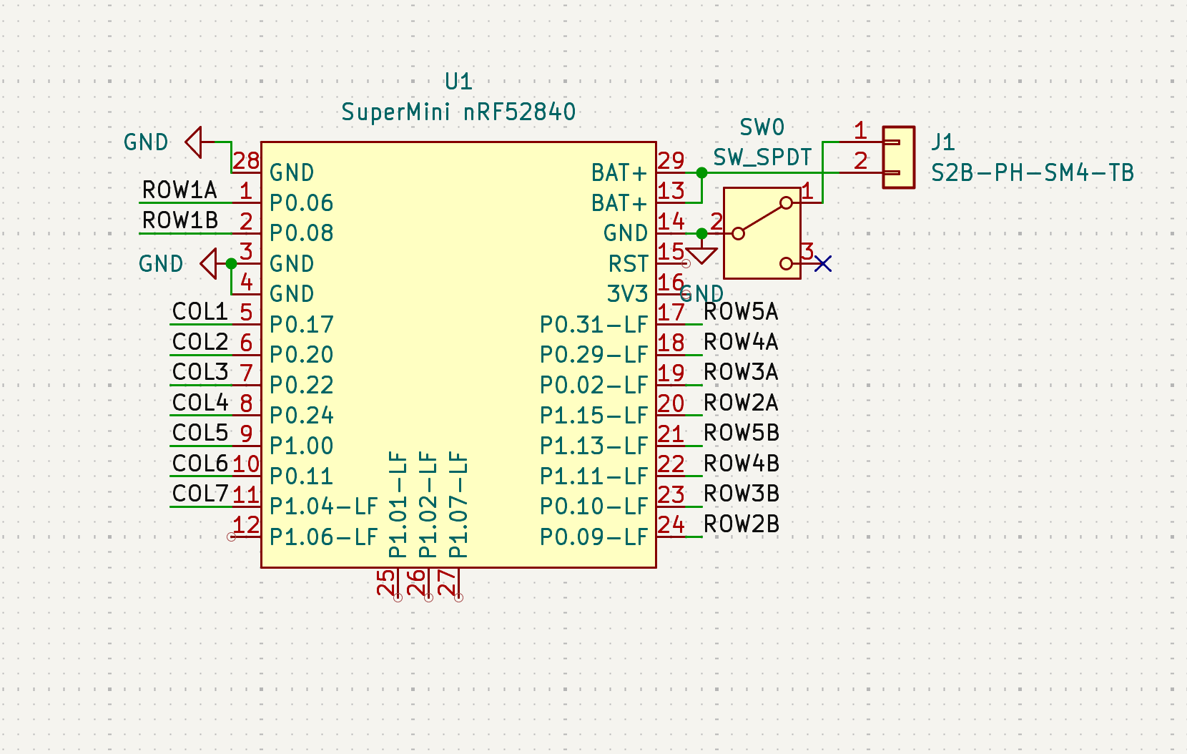
Images/44.png
