Sadrita404/Open-Deck/Images/45.png

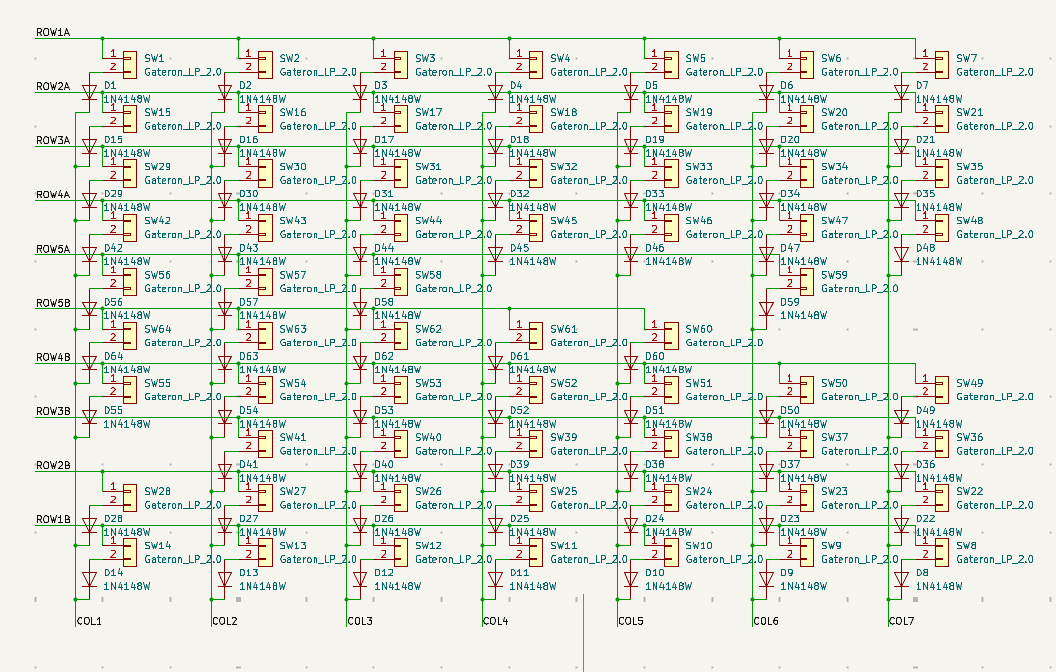
Images/45.png
