Sadrita404/Open-Deck/Images/46.png

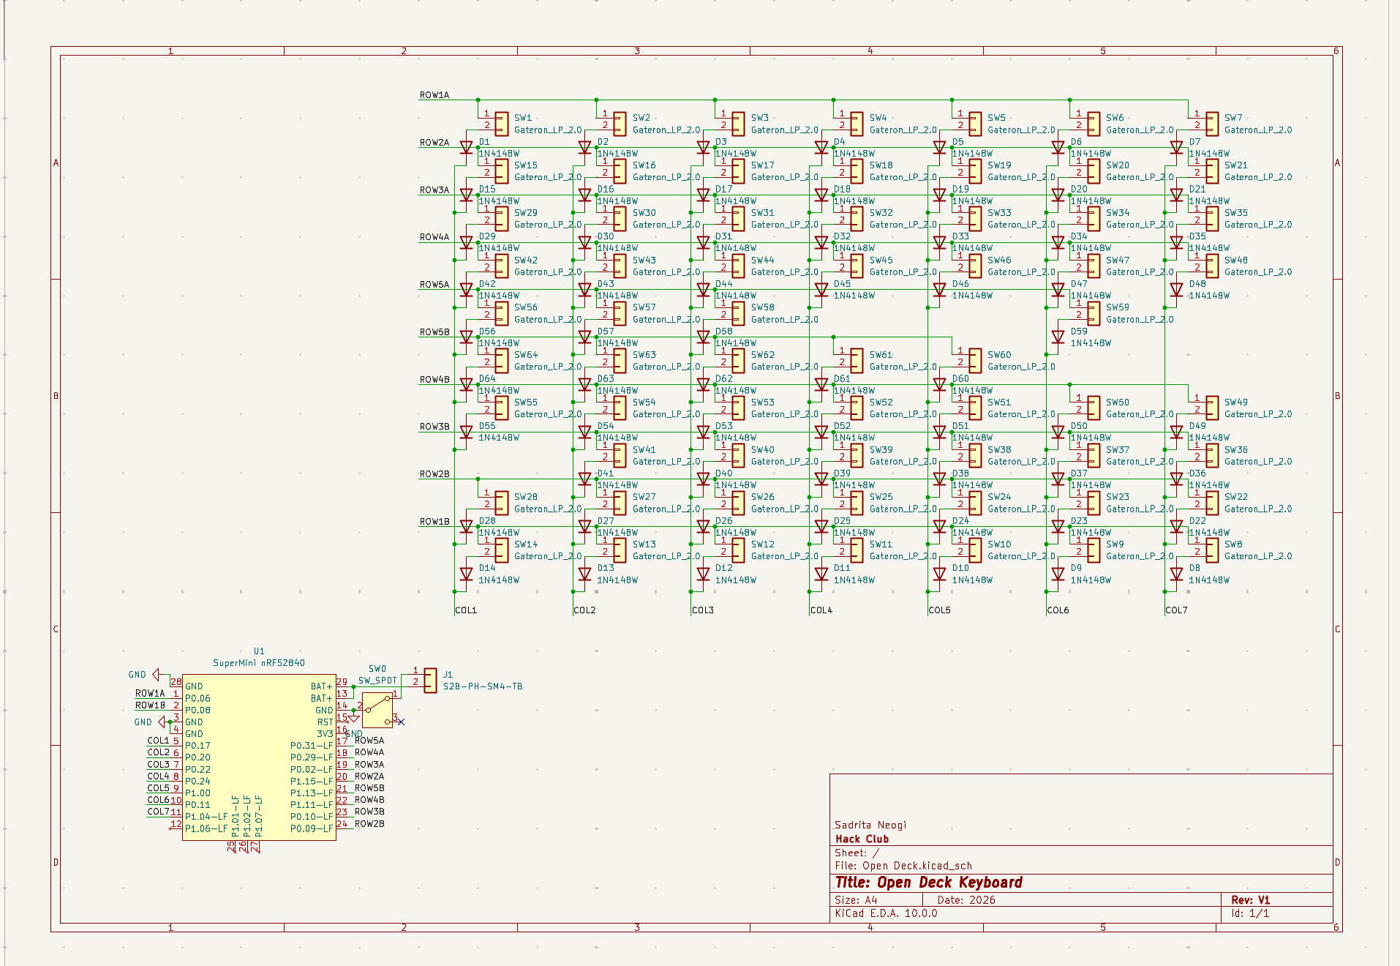
Images/46.png
