Sadrita404/Open-Deck/Images/47.png

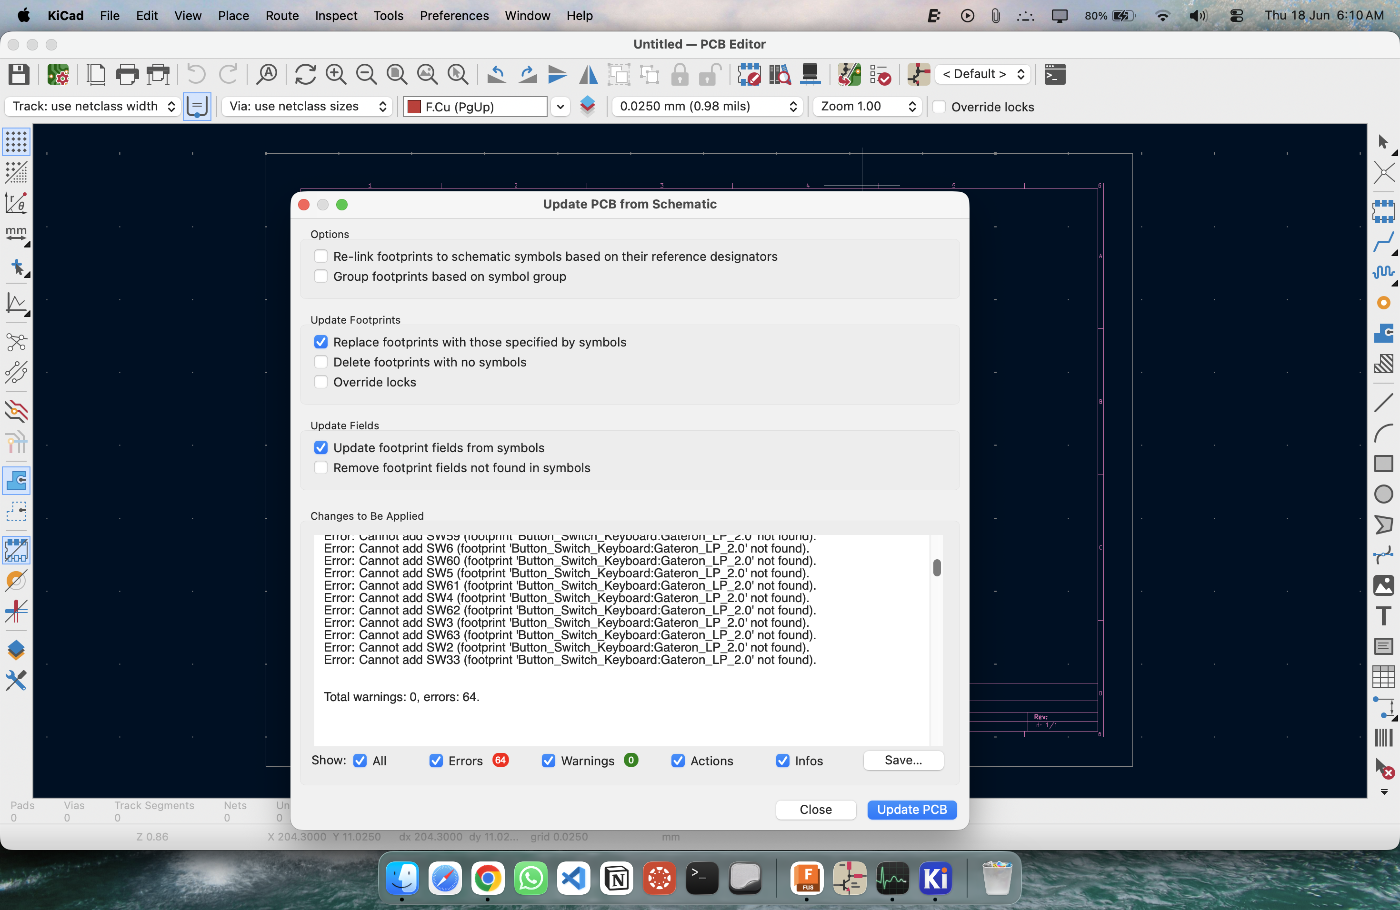
Images/47.png
