Sadrita404/Open-Deck/Images/48.png

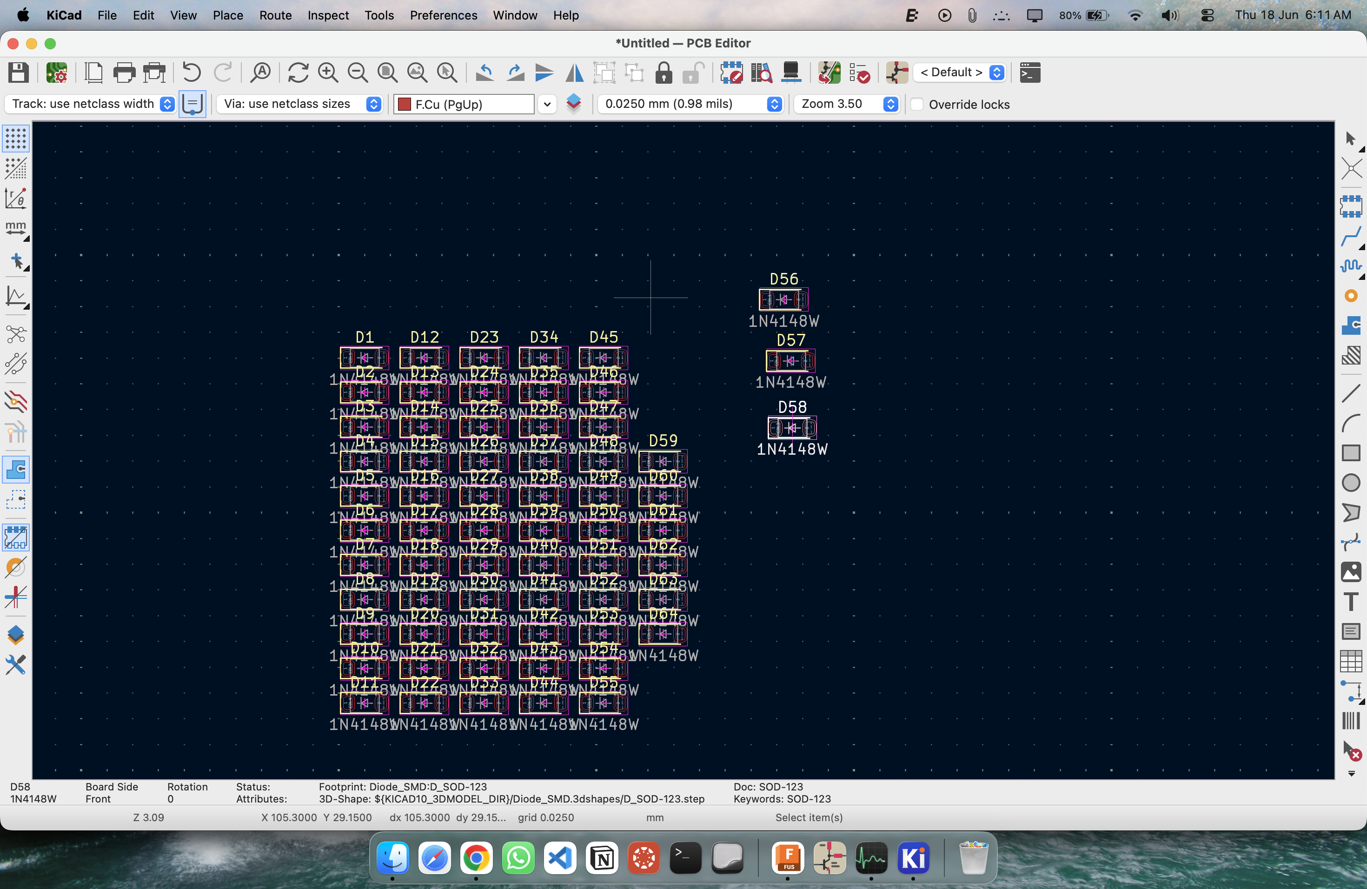
Images/48.png
