Sadrita404/Open-Deck/Images/51.png

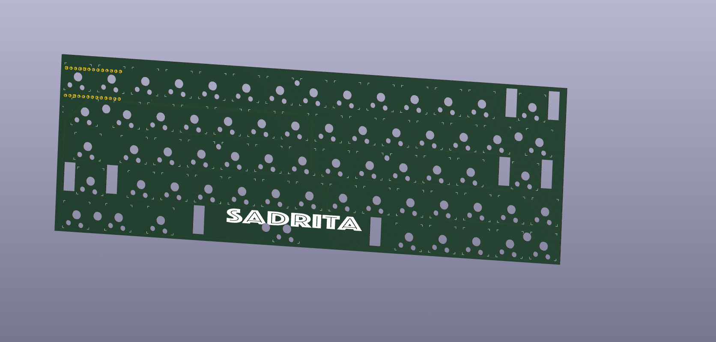
Images/51.png
