Sadrita404/Open-Deck/Images/52.png

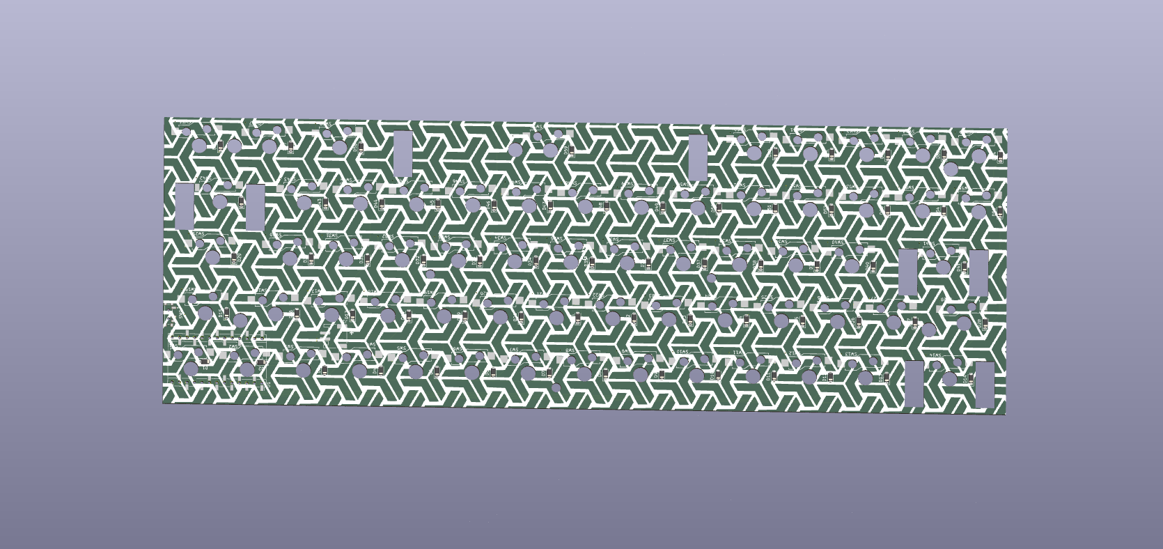
Images/52.png
