Sadrita404/Open-Deck/Images/54.png

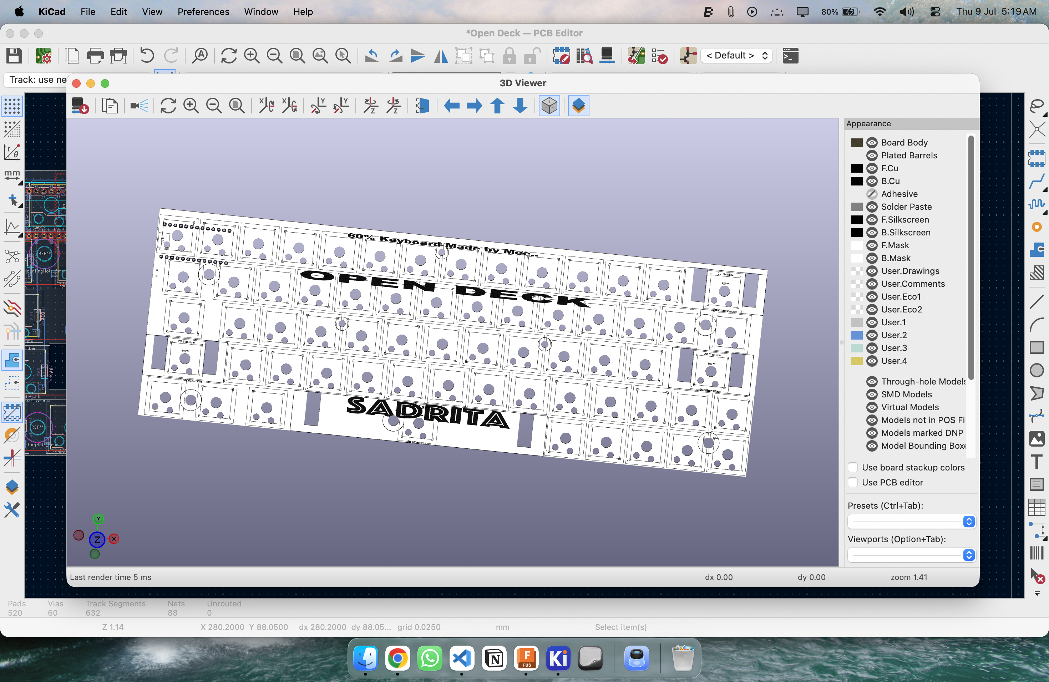
Images/54.png
