Sadrita404/Open-Deck/Renders/Render 1.png

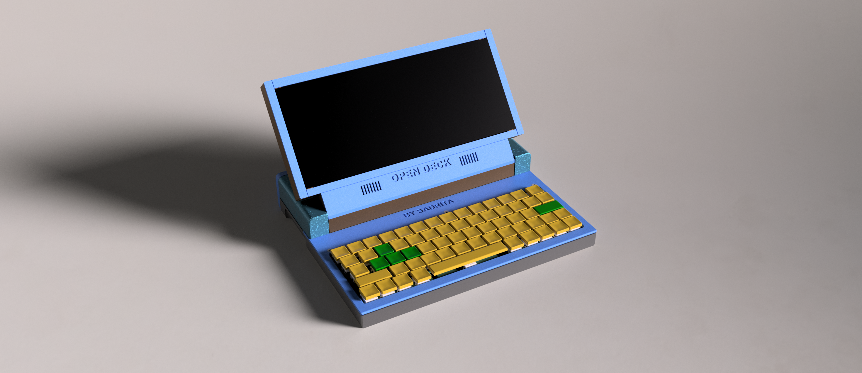
Renders/Render 1.png
