Sadrita404/Open-Deck/Renders/Render 3.png

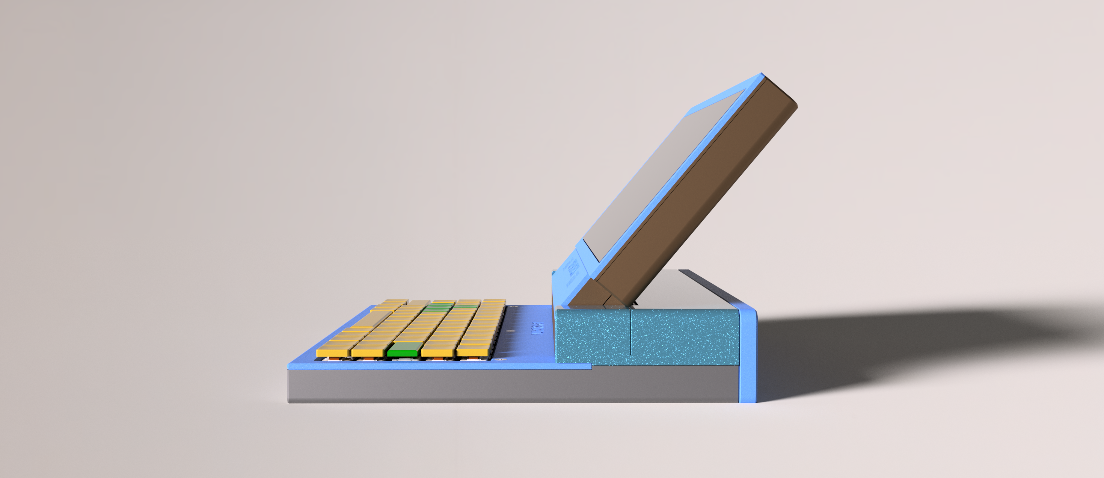
Renders/Render 3.png
