Sadrita404/Open-Deck/Renders/Render 4.png

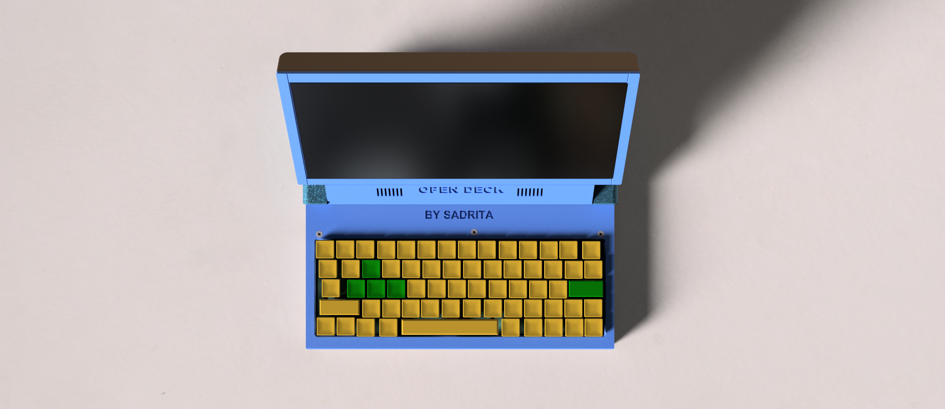
Renders/Render 4.png
