Sadrita404/Open-Deck/Renders/Render 6.png

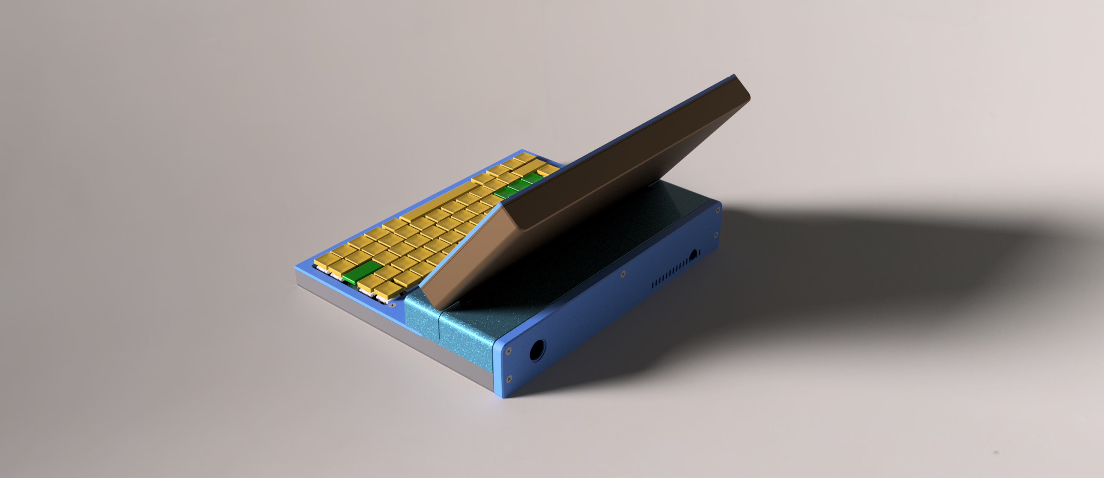
Renders/Render 6.png
