Sadrita404/Open-Deck/Printed Parts/keyboard-plate.stl

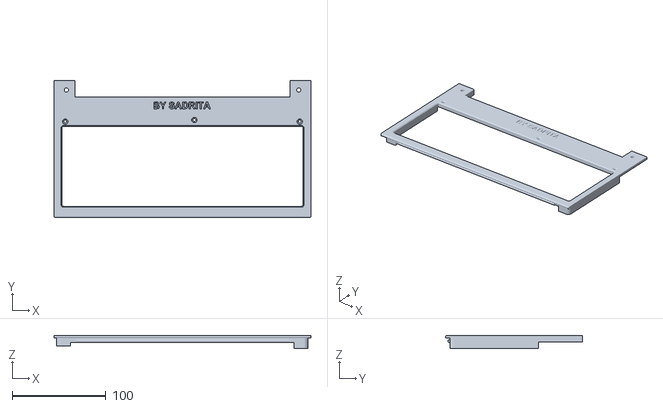
[picture p70: CAD file, 2026-07-08]
Printed Parts/keyboard-plate.stl
274.0 x 146.4 x 14.0
